cbalint13/m-blanc/hardware/mblanc_v0.3/kicad/m-blanc/3d-models/S25HL512TFANHI010.stp

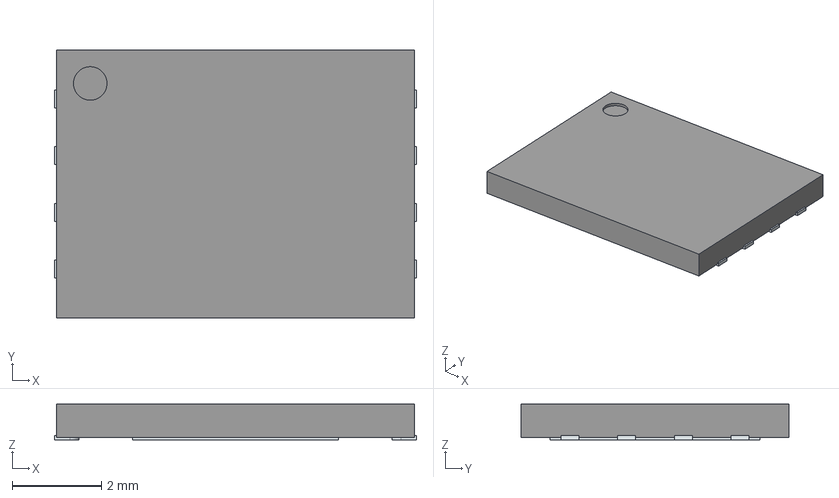
[picture p28: CAD file, 2022-12-04]
hardware/mblanc_v0.3/kicad/m-blanc/3d-models/S25HL512TFANHI010.stp
8.10 x 6.00 x 0.8 mm
ThermalPin
PinsArrayLR
