cbalint13/m-blanc/hardware/mblanc_v0.3/kicad/m-blanc/3d-models/step_temp.STEP

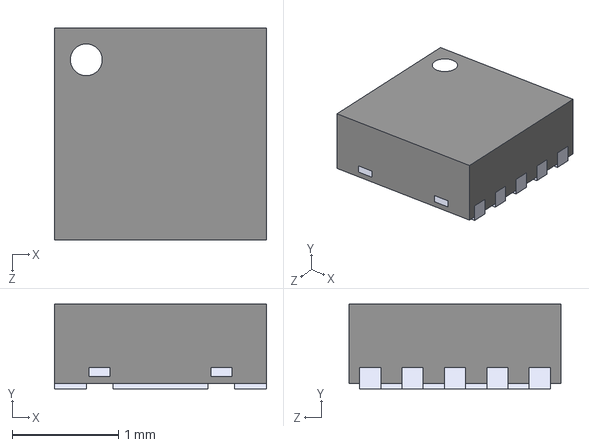
[picture p29: CAD file, 2022-12-04]
hardware/mblanc_v0.3/kicad/m-blanc/3d-models/step_temp.STEP
2.00 x 0.8 x 2.00 mm
