cbalint13/m-blanc/hardware/mblanc_v0.3/kicad/m-blanc/3d-models/74750-0021.stp

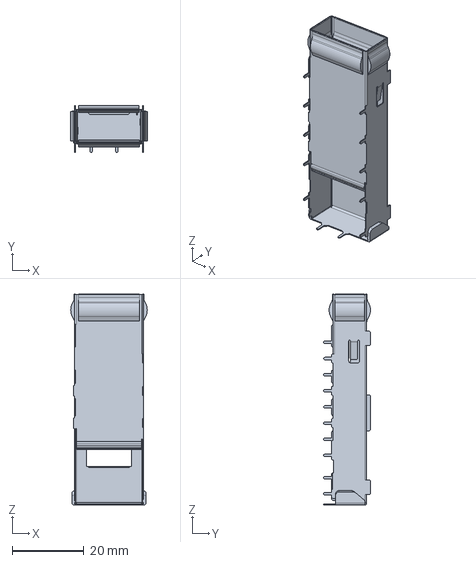
[picture p30: CAD file, 2022-12-04]
hardware/mblanc_v0.3/kicad/m-blanc/3d-models/74750-0021.stp
21.3 x 13.1 x 58.8 mm
