cbalint13/m-blanc/hardware/mblanc_v0.3/kicad/m-blanc/3d-models/296409204003856+.stp

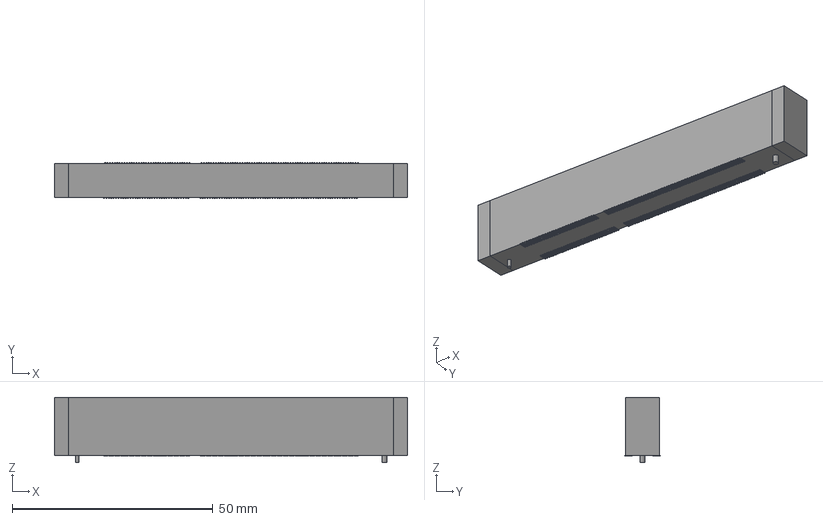
[picture p31: CAD file, 2022-12-04]
hardware/mblanc_v0.3/kicad/m-blanc/3d-models/296409204003856+.stp
88.0 x 8.93 x 16.3 mm
Pins
Lugs x 2
