cbalint13/m-blanc/hardware/mblanc_v0.3/kicad/m-blanc/schematic/2-MEMORY.kicad_sch

## KiCad design hardware/mblanc_v0.3/kicad/m-blanc/schematic/2-MEMORY.kicad_sch (2022-12-04)

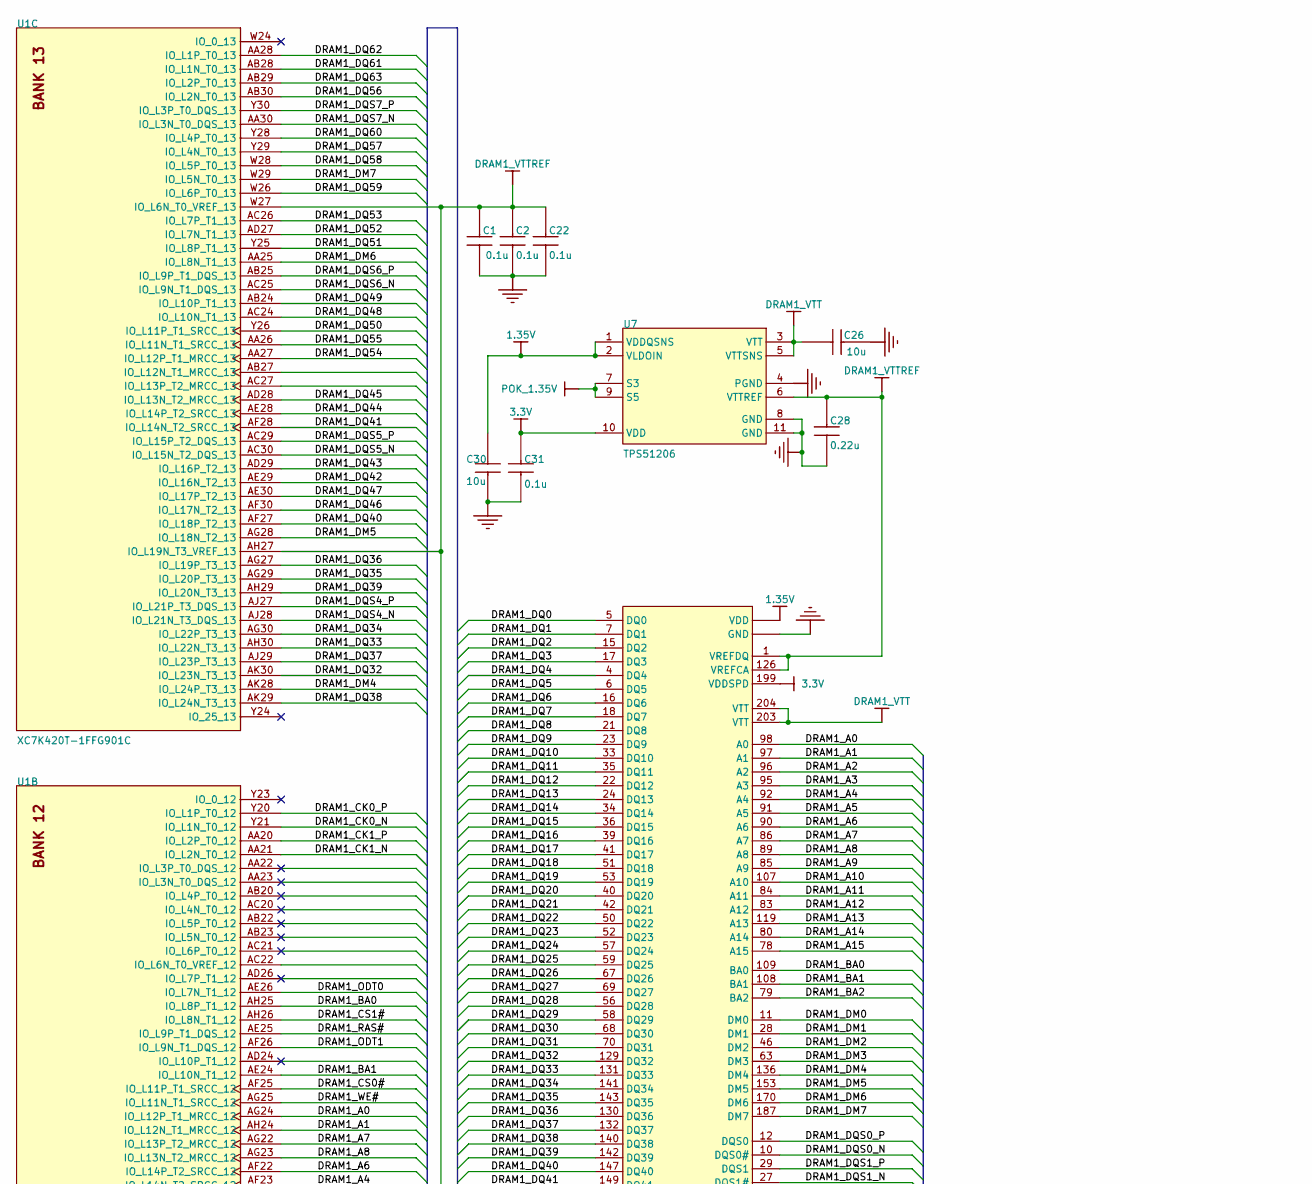
[picture p45: schematic 2-MEMORY.kicad_sch, part in row 1, column 1]

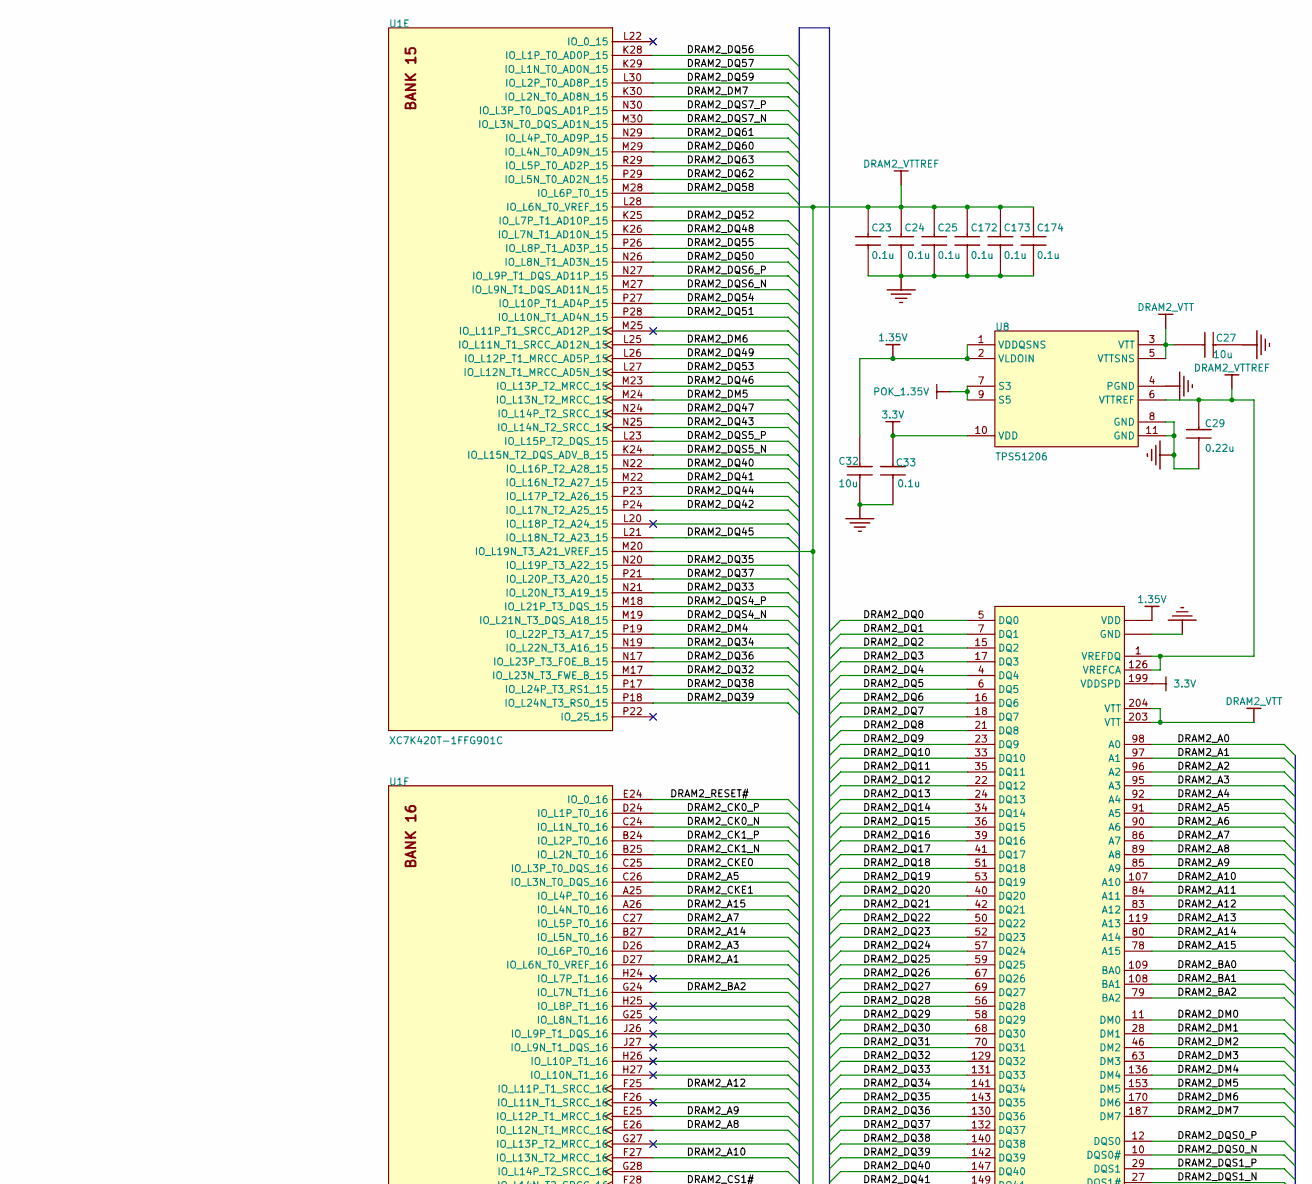
[picture p46: schematic 2-MEMORY.kicad_sch, part in row 1, column 2]

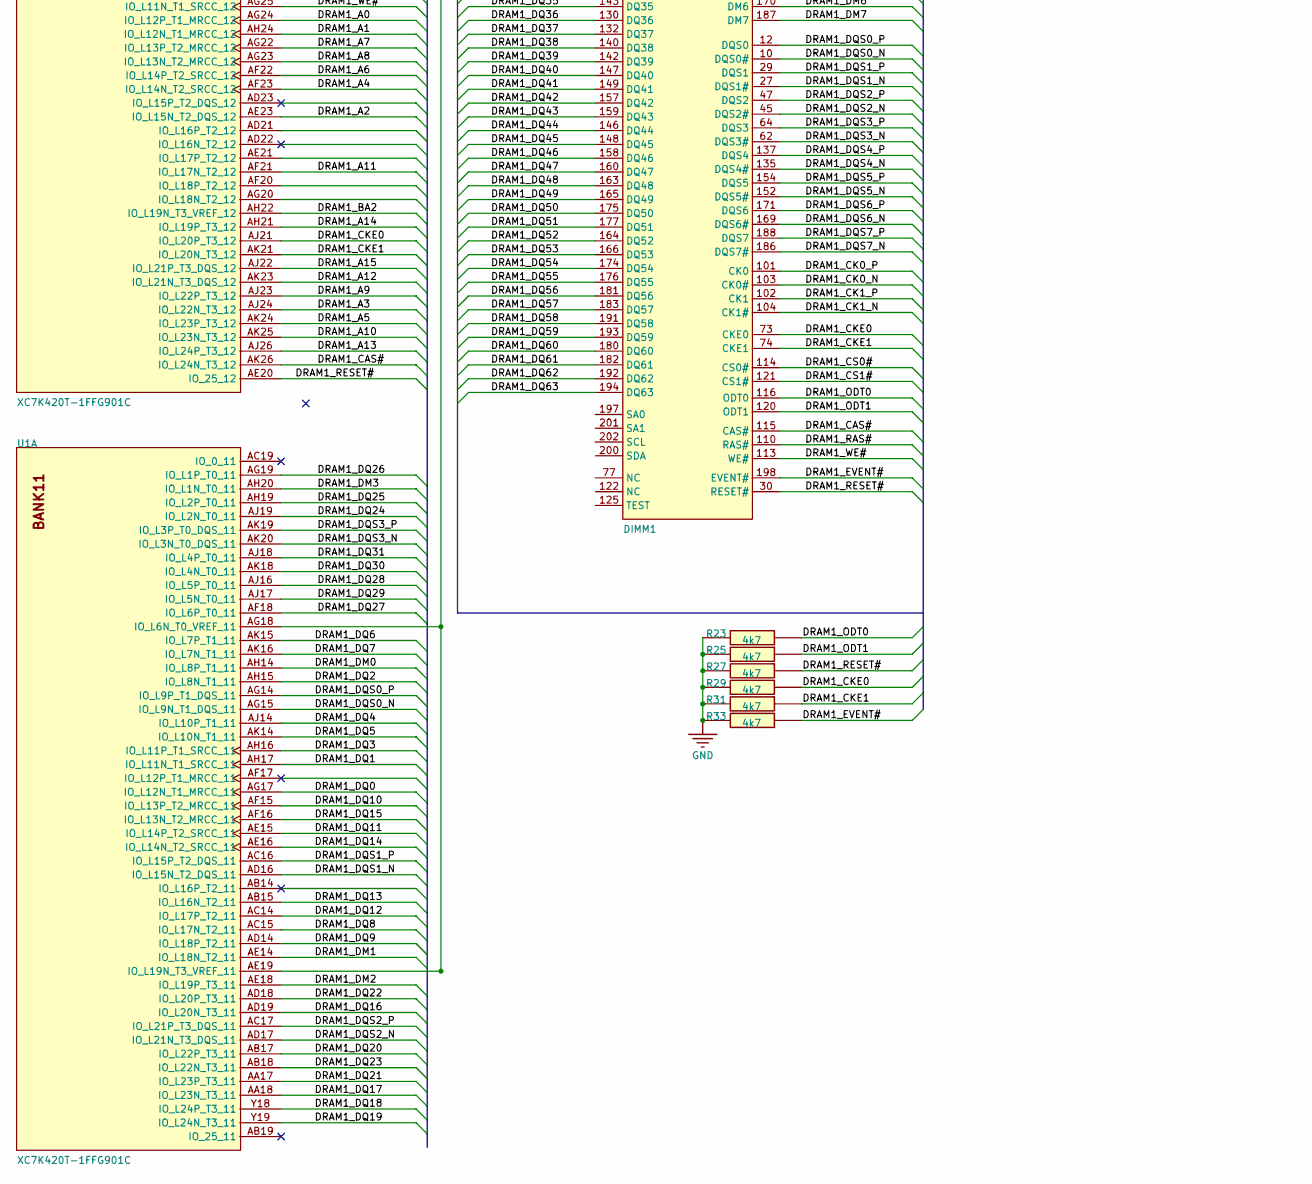
[picture p47: schematic 2-MEMORY.kicad_sch, part in row 2, column 1]

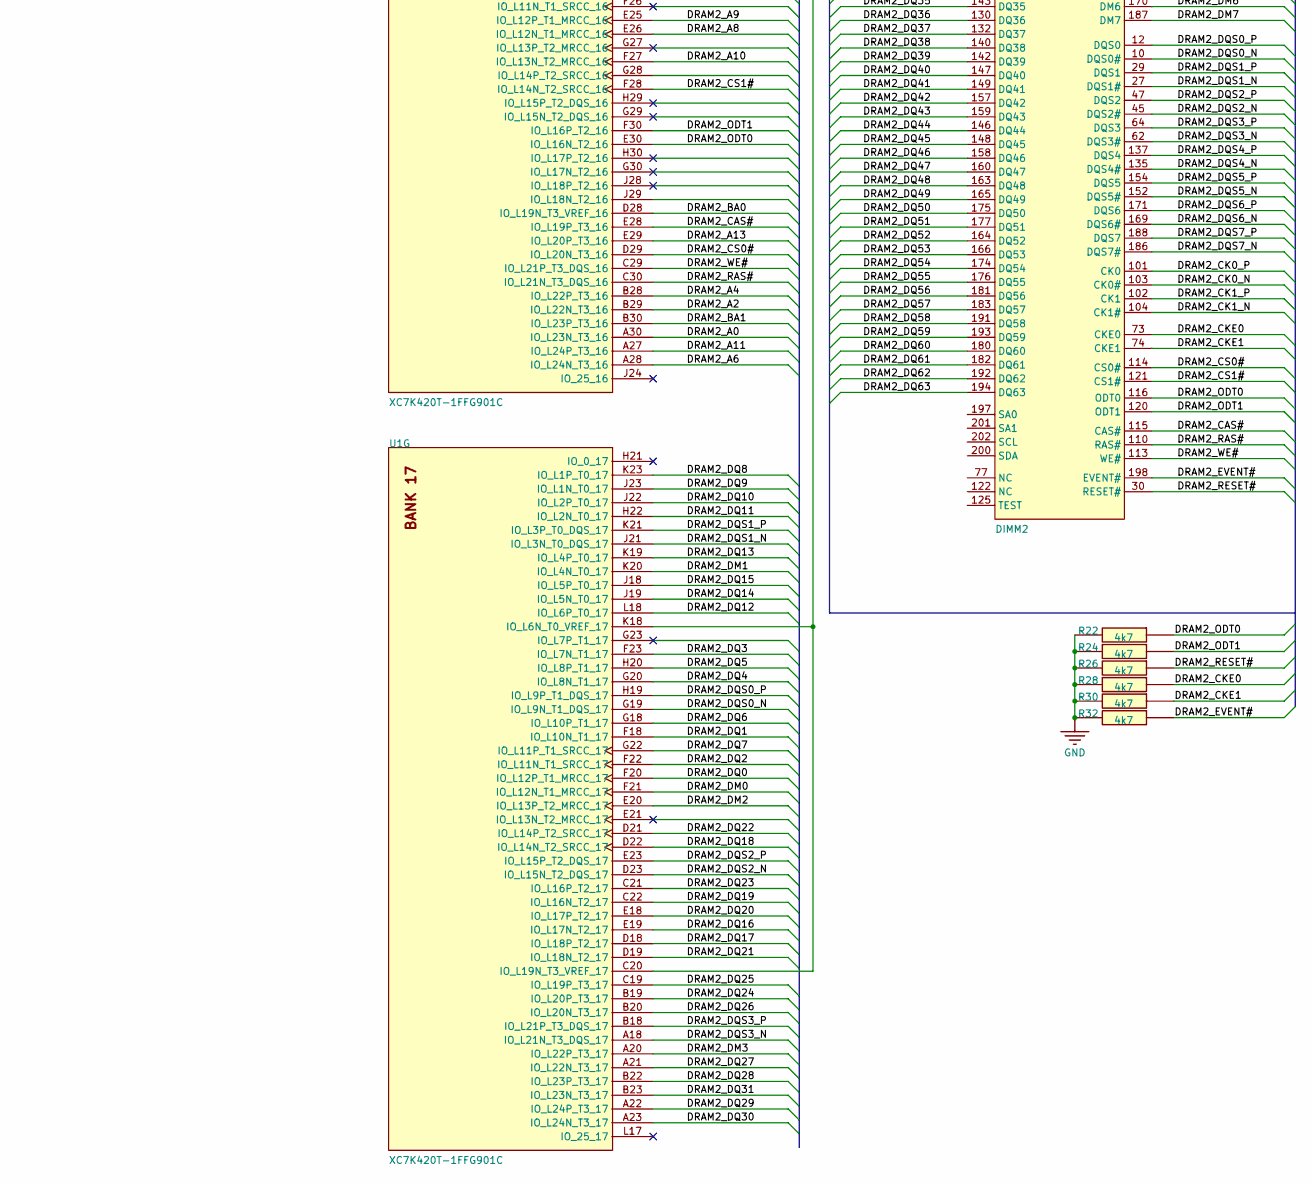
[picture p48: schematic 2-MEMORY.kicad_sch, part in row 2, column 2]

Parts:
C1, C2, C22, C23, C24, C25, C31, C33, C172, C173, C174: 0.1u; SMD0402
C26, C27, C30, C32: 10u; SMD0402
C28, C29: 0.22u; SMD0402
DIMM1, DIMM2: DDR3; 296409204003856
R22, R23, R24, R25, R26, R27, R28, R29, R30, R31, R32, R33: 4k7; SMD0402
U1: XC7K420T-1FFG901C; FFG901; PARTNUMBER XC7K420T-1FFG901C
U7, U8: TPS51206; SON40P200X200X80-11N

Connections:
DRAM1_A0: DIMM1.98 (A0)
DRAM1_A1: DIMM1.97 (A1)
DRAM1_A2: DIMM1.96 (A2)
DRAM1_A3: DIMM1.95 (A3)
DRAM1_A4: DIMM1.92 (A4)
DRAM1_A5: DIMM1.91 (A5)
DRAM1_A6: DIMM1.90 (A6)
DRAM1_A8: DIMM1.89 (A8)
DRAM1_A9: DIMM1.85 (A9)
DRAM1_A10: DIMM1.107 (A10)
DRAM1_A11: DIMM1.84 (A11)
DRAM1_A12: DIMM1.83 (A12)
DRAM1_A13: DIMM1.119 (A13)
DRAM1_A14: DIMM1.80 (A14)
DRAM1_A15: DIMM1.78 (A15)
DRAM1_BA0: DIMM1.109 (BA0)
DRAM1_BA1: DIMM1.108 (BA1)
DRAM1_BA2: DIMM1.79 (BA2)
DRAM1_CKE0: R29.1
DRAM1_CKE1: R31.1
DRAM1_DM0: DIMM1.11 (DM0)
DRAM1_DM1: DIMM1.28 (DM1)
DRAM1_DM2: DIMM1.46 (DM2)
DRAM1_DM3: DIMM1.63 (DM3)
DRAM1_DM4: DIMM1.136 (DM4), U1.AK28 (IO_L24P_T3_13)
DRAM1_DM5: DIMM1.153 (DM5)
DRAM1_DM6: DIMM1.170 (DM6), U1.AA25 (IO_L8N_T1_13)
DRAM1_DM7: DIMM1.187 (DM7), U1.W29 (IO_L5N_T0_13)
DRAM1_DQ0: DIMM1.5 (DQ0)
DRAM1_DQ1: DIMM1.7 (DQ1)
DRAM1_DQ2: DIMM1.15 (DQ2)
DRAM1_DQ3: DIMM1.17 (DQ3)
DRAM1_DQ4: DIMM1.4 (DQ4)
DRAM1_DQ5: DIMM1.6 (DQ5)
DRAM1_DQ6: DIMM1.16 (DQ6)
DRAM1_DQ7: DIMM1.18 (DQ7)
DRAM1_DQ8: DIMM1.21 (DQ8)
DRAM1_DQ9: DIMM1.23 (DQ9)
DRAM1_DQ10: DIMM1.33 (DQ10)
DRAM1_DQ11: DIMM1.35 (DQ11)
DRAM1_DQ12: DIMM1.22 (DQ12)
DRAM1_DQ13: DIMM1.24 (DQ13)
DRAM1_DQ14: DIMM1.34 (DQ14)
DRAM1_DQ15: DIMM1.36 (DQ15)
DRAM1_DQ16: DIMM1.39 (DQ16)
DRAM1_DQ17: DIMM1.41 (DQ17)
DRAM1_DQ18: DIMM1.51 (DQ18)
DRAM1_DQ19: DIMM1.53 (DQ19)
DRAM1_DQ20: DIMM1.40 (DQ20)
DRAM1_DQ21: DIMM1.42 (DQ21)
DRAM1_DQ22: DIMM1.50 (DQ22)
DRAM1_DQ23: DIMM1.52 (DQ23)
DRAM1_DQ24: DIMM1.57 (DQ24)
DRAM1_DQ25: DIMM1.59 (DQ25)
DRAM1_DQ26: DIMM1.67 (DQ26)
DRAM1_DQ27: DIMM1.69 (DQ27)
DRAM1_DQ28: DIMM1.56 (DQ28)
DRAM1_DQ29: DIMM1.58 (DQ29)
DRAM1_DQ30: DIMM1.68 (DQ30)
DRAM1_DQ31: DIMM1.70 (DQ31)
DRAM1_DQ32: DIMM1.129 (DQ32), U1.AK30 (IO_L23N_T3_13)
DRAM1_DQ33: DIMM1.131 (DQ33), U1.AH30 (IO_L22N_T3_13)
DRAM1_DQ34: DIMM1.141 (DQ34), U1.AG30 (IO_L22P_T3_13)
DRAM1_DQ35: DIMM1.143 (DQ35), U1.AG29 (IO_L20P_T3_13)
DRAM1_DQ36: DIMM1.130 (DQ36)
DRAM1_DQ37: DIMM1.132 (DQ37), U1.AJ29 (IO_L23P_T3_13)
DRAM1_DQ38: DIMM1.140 (DQ38), U1.AK29 (IO_L24N_T3_13)
DRAM1_DQ39: DIMM1.142 (DQ39), U1.AH29 (IO_L20N_T3_13)
DRAM1_DQ40: DIMM1.147 (DQ40), U1.AF27 (IO_L18P_T2_13)
DRAM1_DQ41: DIMM1.149 (DQ41), U1.AF28 (IO_L14N_T2_SRCC_13)
DRAM1_DQ42: DIMM1.157 (DQ42), U1.AE29 (IO_L16N_T2_13)
DRAM1_DQ43: DIMM1.159 (DQ43), U1.AD29 (IO_L16P_T2_13)
DRAM1_DQ44: DIMM1.146 (DQ44), U1.AE28 (IO_L14P_T2_SRCC_13)
DRAM1_DQ45: U1.AD28 (IO_L13N_T2_MRCC_13)
DRAM1_DQ46: U1.AF30 (IO_L17N_T2_13)
DRAM1_DQ47: U1.AE30 (IO_L17P_T2_13)
DRAM1_DQ48: U1.AC24 (IO_L10N_T1_13)
DRAM1_DQ49: U1.AB24 (IO_L10P_T1_13)
DRAM1_DQ50: U1.Y26 (IO_L11P_T1_SRCC_13)
DRAM1_DQ51: U1.Y25 (IO_L8P_T1_13)
DRAM1_DQ53: U1.AC26 (IO_L7P_T1_13)
DRAM1_DQ54: U1.AA27 (IO_L12P_T1_MRCC_13)
DRAM1_DQ55: U1.AA26 (IO_L11N_T1_SRCC_13)
DRAM1_DQ56: U1.AB30 (IO_L2N_T0_13)
DRAM1_DQ57: U1.Y29 (IO_L4N_T0_13)
DRAM1_DQ58: U1.W28 (IO_L5P_T0_13)
DRAM1_DQ59: U1.W26 (IO_L6P_T0_13)
DRAM1_DQ60: U1.Y28 (IO_L4P_T0_13)
DRAM1_DQ61: U1.AB28 (IO_L1N_T0_13)
DRAM1_DQ62: U1.AA28 (IO_L1P_T0_13)
DRAM1_DQ63: U1.AB29 (IO_L2P_T0_13)
DRAM1_DQS0_N: DIMM1.10 (DQS0#)
DRAM1_DQS0_P: DIMM1.12 (DQS0)
DRAM1_DQS1_N: DIMM1.27 (DQS1#)
DRAM1_DQS1_P: DIMM1.29 (DQS1)
DRAM1_DQS2_N: DIMM1.45 (DQS2#)
DRAM1_DQS2_P: DIMM1.47 (DQS2)
DRAM1_DQS3_N: DIMM1.62 (DQS3#)
DRAM1_DQS3_P: DIMM1.64 (DQS3)
DRAM1_DQS4_N: U1.AJ28 (IO_L21N_T3_DQS_13)
DRAM1_DQS4_P: U1.AJ27 (IO_L21P_T3_DQS_13)
DRAM1_DQS5_N: U1.AC30 (IO_L15N_T2_DQS_13)
DRAM1_DQS5_P: U1.AC29 (IO_L15P_T2_DQS_13)
DRAM1_DQS6_N: U1.AC25 (IO_L9N_T1_DQS_13)
DRAM1_DQS6_P: U1.AB25 (IO_L9P_T1_DQS_13)
DRAM1_DQS7_N: U1.AA30 (IO_L3N_T0_DQS_13)
DRAM1_DQS7_P: U1.Y30 (IO_L3P_T0_DQS_13)
DRAM1_EVENT#: R33.1
DRAM1_ODT0: R23.1
DRAM1_ODT1: R25.1
DRAM1_RESET#: R27.1
DRAM2_A0: DIMM2.98 (A0), U1.A30 (IO_L23N_T3_16)
DRAM2_A1: DIMM2.97 (A1), U1.D27 (IO_L6N_T0_VREF_16)
DRAM2_A2: DIMM2.96 (A2), U1.B29 (IO_L22N_T3_16)
DRAM2_A3: DIMM2.95 (A3), U1.D26 (IO_L6P_T0_16)
DRAM2_A4: DIMM2.92 (A4), U1.B28 (IO_L22P_T3_16)
DRAM2_A5: DIMM2.91 (A5), U1.C26 (IO_L3N_T0_DQS_16)
DRAM2_A6: DIMM2.90 (A6), U1.A28 (IO_L24N_T3_16)
DRAM2_A7: DIMM2.86 (A7), U1.C27 (IO_L5P_T0_16)
DRAM2_A8: DIMM2.89 (A8), U1.E26 (IO_L12N_T1_MRCC_16)
DRAM2_A9: DIMM2.85 (A9), U1.E25 (IO_L12P_T1_MRCC_16)
DRAM2_A10: DIMM2.107 (A10), U1.F27 (IO_L13N_T2_MRCC_16)
DRAM2_A11: DIMM2.84 (A11), U1.A27 (IO_L24P_T3_16)
DRAM2_A12: DIMM2.83 (A12), U1.F25 (IO_L11P_T1_SRCC_16)
DRAM2_A13: DIMM2.119 (A13), U1.E29 (IO_L20P_T3_16)
DRAM2_A14: DIMM2.80 (A14), U1.B27 (IO_L5N_T0_16)
DRAM2_A15: DIMM2.78 (A15), U1.A26 (IO_L4N_T0_16)
DRAM2_BA0: DIMM2.109 (BA0), U1.D28 (IO_L19N_T3_VREF_16)
DRAM2_BA1: DIMM2.108 (BA1), U1.B30 (IO_L23P_T3_16)
DRAM2_BA2: DIMM2.79 (BA2), U1.G24 (IO_L7N_T1_16)
DRAM2_CAS#: DIMM2.115 (CAS#), U1.E28 (IO_L19P_T3_16)
DRAM2_CK0_N: DIMM2.103 (CK0#), U1.C24 (IO_L1N_T0_16)
DRAM2_CK0_P: DIMM2.101 (CK0), U1.D24 (IO_L1P_T0_16)
DRAM2_CK1_N: DIMM2.104 (CK1#), U1.B25 (IO_L2N_T0_16)
DRAM2_CK1_P: DIMM2.102 (CK1), U1.B24 (IO_L2P_T0_16)
DRAM2_CKE0: DIMM2.73 (CKE0), R28.1, U1.C25 (IO_L3P_T0_DQS_16)
DRAM2_CKE1: DIMM2.74 (CKE1), R30.1, U1.A25 (IO_L4P_T0_16)
DRAM2_CS0#: DIMM2.114 (CS0#), U1.D29 (IO_L20N_T3_16)
DRAM2_CS1#: DIMM2.121 (CS1#), U1.F28 (IO_L14N_T2_SRCC_16)
DRAM2_DM0: DIMM2.11 (DM0)
DRAM2_DM1: DIMM2.28 (DM1)
DRAM2_DM2: DIMM2.46 (DM2)
DRAM2_DM3: DIMM2.63 (DM3)
DRAM2_DM4: DIMM2.136 (DM4), U1.P19 (IO_L22P_T3_A17_15)
DRAM2_DM5: DIMM2.153 (DM5), U1.M24 (IO_L13N_T2_MRCC_15)
DRAM2_DM6: DIMM2.170 (DM6), U1.L25 (IO_L11N_T1_SRCC_AD12N_15)
DRAM2_DM7: DIMM2.187 (DM7), U1.K30 (IO_L2N_T0_AD8N_15)
DRAM2_DQ0: DIMM2.5 (DQ0)
DRAM2_DQ1: DIMM2.7 (DQ1)
DRAM2_DQ2: DIMM2.15 (DQ2)
DRAM2_DQ3: DIMM2.17 (DQ3)
DRAM2_DQ4: DIMM2.4 (DQ4)
DRAM2_DQ5: DIMM2.6 (DQ5)
DRAM2_DQ6: DIMM2.16 (DQ6)
DRAM2_DQ7: DIMM2.18 (DQ7)
DRAM2_DQ8: DIMM2.21 (DQ8)
DRAM2_DQ9: DIMM2.23 (DQ9)
DRAM2_DQ10: DIMM2.33 (DQ10)
DRAM2_DQ11: DIMM2.35 (DQ11)
DRAM2_DQ12: DIMM2.22 (DQ12)
DRAM2_DQ13: DIMM2.24 (DQ13)
DRAM2_DQ14: DIMM2.34 (DQ14)
DRAM2_DQ15: DIMM2.36 (DQ15)
DRAM2_DQ16: DIMM2.39 (DQ16)
DRAM2_DQ17: DIMM2.41 (DQ17)
DRAM2_DQ18: DIMM2.51 (DQ18)
DRAM2_DQ19: DIMM2.53 (DQ19)
DRAM2_DQ20: DIMM2.40 (DQ20)
DRAM2_DQ21: DIMM2.42 (DQ21)
DRAM2_DQ22: DIMM2.50 (DQ22)
DRAM2_DQ23: DIMM2.52 (DQ23)
DRAM2_DQ24: DIMM2.57 (DQ24)
DRAM2_DQ25: DIMM2.59 (DQ25)
DRAM2_DQ26: DIMM2.67 (DQ26)
DRAM2_DQ27: DIMM2.69 (DQ27)
DRAM2_DQ28: DIMM2.56 (DQ28)
DRAM2_DQ29: DIMM2.58 (DQ29)
DRAM2_DQ30: DIMM2.68 (DQ30)
DRAM2_DQ31: DIMM2.70 (DQ31)
DRAM2_DQ32: DIMM2.129 (DQ32), U1.M17 (IO_L23N_T3_FWE_B_15)
DRAM2_DQ33: DIMM2.131 (DQ33), U1.N21 (IO_L20N_T3_A19_15)
DRAM2_DQ34: DIMM2.141 (DQ34), U1.N19 (IO_L22N_T3_A16_15)
DRAM2_DQ35: DIMM2.143 (DQ35), U1.N20 (IO_L19P_T3_A22_15)
DRAM2_DQ36: DIMM2.130 (DQ36), U1.N17 (IO_L23P_T3_FOE_B_15)
DRAM2_DQ37: DIMM2.132 (DQ37), U1.P21 (IO_L20P_T3_A20_15)
DRAM2_DQ38: DIMM2.140 (DQ38), U1.P17 (IO_L24P_T3_RS1_15)
DRAM2_DQ39: DIMM2.142 (DQ39), U1.P18 (IO_L24N_T3_RS0_15)
DRAM2_DQ40: DIMM2.147 (DQ40), U1.N22 (IO_L16P_T2_A28_15)
DRAM2_DQ41: DIMM2.149 (DQ41), U1.M22 (IO_L16N_T2_A27_15)
DRAM2_DQ42: DIMM2.157 (DQ42), U1.P24 (IO_L17N_T2_A25_15)
DRAM2_DQ43: DIMM2.159 (DQ43), U1.N25 (IO_L14N_T2_SRCC_15)
DRAM2_DQ44: DIMM2.146 (DQ44), U1.P23 (IO_L17P_T2_A26_15)
DRAM2_DQ45: DIMM2.148 (DQ45), U1.L21 (IO_L18N_T2_A23_15)
DRAM2_DQ46: DIMM2.158 (DQ46), U1.M23 (IO_L13P_T2_MRCC_15)
DRAM2_DQ47: DIMM2.160 (DQ47), U1.N24 (IO_L14P_T2_SRCC_15)
DRAM2_DQ48: DIMM2.163 (DQ48), U1.K26 (IO_L7N_T1_AD10N_15)
DRAM2_DQ49: DIMM2.165 (DQ49), U1.L26 (IO_L12P_T1_MRCC_AD5P_15)
DRAM2_DQ50: DIMM2.175 (DQ50), U1.N26 (IO_L8N_T1_AD3N_15)
DRAM2_DQ51: DIMM2.177 (DQ51), U1.P28 (IO_L10N_T1_AD4N_15)
DRAM2_DQ52: DIMM2.164 (DQ52), U1.K25 (IO_L7P_T1_AD10P_15)
DRAM2_DQ53: DIMM2.166 (DQ53)
DRAM2_DQ54: DIMM2.174 (DQ54), U1.P27 (IO_L10P_T1_AD4P_15)
DRAM2_DQ55: DIMM2.176 (DQ55), U1.P26 (IO_L8P_T1_AD3P_15)
DRAM2_DQ56: DIMM2.181 (DQ56), U1.K28 (IO_L1P_T0_AD0P_15)
DRAM2_DQ57: DIMM2.183 (DQ57), U1.K29 (IO_L1N_T0_AD0N_15)
DRAM2_DQ58: DIMM2.191 (DQ58), U1.M28 (IO_L6P_T0_15)
DRAM2_DQ59: DIMM2.193 (DQ59), U1.L30 (IO_L2P_T0_AD8P_15)
DRAM2_DQ60: DIMM2.180 (DQ60), U1.M29 (IO_L4N_T0_AD9N_15)
DRAM2_DQ61: DIMM2.182 (DQ61), U1.N29 (IO_L4P_T0_AD9P_15)
DRAM2_DQ62: DIMM2.192 (DQ62), U1.P29 (IO_L5N_T0_AD2N_15)
DRAM2_DQ63: DIMM2.194 (DQ63), U1.R29 (IO_L5P_T0_AD2P_15)
DRAM2_DQS0_N: DIMM2.10 (DQS0#)
DRAM2_DQS0_P: DIMM2.12 (DQS0)
DRAM2_DQS1_N: DIMM2.27 (DQS1#)
DRAM2_DQS1_P: DIMM2.29 (DQS1)
DRAM2_DQS2_N: DIMM2.45 (DQS2#)
DRAM2_DQS2_P: DIMM2.47 (DQS2)
DRAM2_DQS3_N: DIMM2.62 (DQS3#)
DRAM2_DQS3_P: DIMM2.64 (DQS3)
DRAM2_DQS4_N: DIMM2.135 (DQS4#), U1.M19 (IO_L21N_T3_DQS_A18_15)
DRAM2_DQS4_P: DIMM2.137 (DQS4), U1.M18 (IO_L21P_T3_DQS_15)
DRAM2_DQS5_N: DIMM2.152 (DQS5#), U1.K24 (IO_L15N_T2_DQS_ADV_B_15)
DRAM2_DQS5_P: DIMM2.154 (DQS5), U1.L23 (IO_L15P_T2_DQS_15)
DRAM2_DQS6_N: DIMM2.169 (DQS6#), U1.M27 (IO_L9N_T1_DQS_AD11N_15)
DRAM2_DQS6_P: DIMM2.171 (DQS6), U1.N27 (IO_L9P_T1_DQS_AD11P_15)
DRAM2_DQS7_N: DIMM2.186 (DQS7#), U1.M30 (IO_L3N_T0_DQS_AD1N_15)
DRAM2_DQS7_P: DIMM2.188 (DQS7), U1.N30 (IO_L3P_T0_DQS_AD1P_15)
DRAM2_EVENT#: DIMM2.198 (EVENT#), R32.1
DRAM2_ODT0: DIMM2.116 (ODT0), R22.1, U1.E30 (IO_L16N_T2_16)
DRAM2_ODT1: DIMM2.120 (ODT1), R24.1, U1.F30 (IO_L16P_T2_16)
DRAM2_RAS#: DIMM2.110 (RAS#), U1.C30 (IO_L21N_T3_DQS_16)
DRAM2_RESET#: DIMM2.30 (RESET#), R26.1, U1.E24 (IO_0_16)
DRAM2_WE#: DIMM2.113 (WE#), U1.C29 (IO_L21P_T3_DQS_16)
unnamed: C1.1, C2.1, C22.1
unnamed: C1.2, C2.2, C22.2, U1.AH27 (IO_L19N_T3_VREF_13), U1.W27 (IO_L6N_T0_VREF_13)
unnamed: C26.1, U7.3 (VTT), U7.5 (VTTSNS)
unnamed: C27.1, U8.3 (VTT), U8.5 (VTTSNS)
unnamed: C28.1, U7.8 (GND), U7.11 (GND)
unnamed: C28.2, DIMM1.1 (VREFDQ), DIMM1.126 (VREFCA), U7.6 (VTTREF)
unnamed: C29.1, U8.8 (GND), U8.11 (GND)
unnamed: C29.2, DIMM2.1 (VREFDQ), DIMM2.126 (VREFCA), U8.6 (VTTREF)
unnamed: C30.1, U7.1 (VDDQSNS), U7.2 (VLDOIN)
unnamed: C30.2, C31.2
unnamed: C31.1, U7.10 (VDD)
unnamed: C32.1, U8.1 (VDDQSNS), U8.2 (VLDOIN)
unnamed: C32.2, C33.2
unnamed: C33.1, U8.10 (VDD)
unnamed: C23.1, C24.1, C25.1, C172.1, C173.1, C174.1
unnamed: C23.2, C24.2, C25.2, C172.2, C173.2, C174.2, U1.L28 (IO_L6N_T0_VREF_15), U1.M20 (IO_L19N_T3_A21_VREF_15)
unnamed: DIMM1.75 (VDD), DIMM1.76 (VDD), DIMM1.81 (VDD), DIMM1.82 (VDD), DIMM1.87 (VDD), DIMM1.88 (VDD), DIMM1.93 (VDD), DIMM1.94 (VDD), DIMM1.99 (VDD), DIMM1.100 (VDD), DIMM1.105 (VDD), DIMM1.106 (VDD), DIMM1.111 (VDD), DIMM1.112 (VDD), DIMM1.117 (VDD), DIMM1.118 (VDD), DIMM1.123 (VDD), DIMM1.124 (VDD)
unnamed: DIMM1.2 (GND), DIMM1.3 (GND), DIMM1.8 (GND), DIMM1.9 (GND), DIMM1.13 (GND), DIMM1.14 (GND), DIMM1.19 (GND), DIMM1.20 (GND), DIMM1.25 (GND), DIMM1.26 (GND), DIMM1.31 (GND), DIMM1.32 (GND), DIMM1.37 (GND), DIMM1.38 (GND), DIMM1.43 (GND), DIMM1.44 (GND), DIMM1.48 (GND), DIMM1.49 (GND), DIMM1.54 (GND), DIMM1.55 (GND), DIMM1.60 (GND), DIMM1.61 (GND), DIMM1.65 (GND), DIMM1.66 (GND), DIMM1.71 (GND), DIMM1.72 (GND), DIMM1.127 (GND), DIMM1.128 (GND), DIMM1.133 (GND), DIMM1.134 (GND), DIMM1.138 (GND), DIMM1.139 (GND), DIMM1.144 (GND), DIMM1.145 (GND), DIMM1.150 (GND), DIMM1.151 (GND), DIMM1.155 (GND), DIMM1.156 (GND), DIMM1.161 (GND), DIMM1.162 (GND), DIMM1.167 (GND), DIMM1.168 (GND), DIMM1.172 (GND), DIMM1.173 (GND), DIMM1.178 (GND), DIMM1.179 (GND), DIMM1.184 (GND), DIMM1.185 (GND), DIMM1.189 (GND), DIMM1.190 (GND), DIMM1.195 (GND), DIMM1.196 (GND)
unnamed: DIMM1.203 (VTT), DIMM1.204 (VTT)
unnamed: DIMM2.75 (VDD), DIMM2.76 (VDD), DIMM2.81 (VDD), DIMM2.82 (VDD), DIMM2.87 (VDD), DIMM2.88 (VDD), DIMM2.93 (VDD), DIMM2.94 (VDD), DIMM2.99 (VDD), DIMM2.100 (VDD), DIMM2.105 (VDD), DIMM2.106 (VDD), DIMM2.111 (VDD), DIMM2.112 (VDD), DIMM2.117 (VDD), DIMM2.118 (VDD), DIMM2.123 (VDD), DIMM2.124 (VDD)
unnamed: DIMM2.2 (GND), DIMM2.3 (GND), DIMM2.8 (GND), DIMM2.9 (GND), DIMM2.13 (GND), DIMM2.14 (GND), DIMM2.19 (GND), DIMM2.20 (GND), DIMM2.25 (GND), DIMM2.26 (GND), DIMM2.31 (GND), DIMM2.32 (GND), DIMM2.37 (GND), DIMM2.38 (GND), DIMM2.43 (GND), DIMM2.44 (GND), DIMM2.48 (GND), DIMM2.49 (GND), DIMM2.54 (GND), DIMM2.55 (GND), DIMM2.60 (GND), DIMM2.61 (GND), DIMM2.65 (GND), DIMM2.66 (GND), DIMM2.71 (GND), DIMM2.72 (GND), DIMM2.127 (GND), DIMM2.128 (GND), DIMM2.133 (GND), DIMM2.134 (GND), DIMM2.138 (GND), DIMM2.139 (GND), DIMM2.144 (GND), DIMM2.145 (GND), DIMM2.150 (GND), DIMM2.151 (GND), DIMM2.155 (GND), DIMM2.156 (GND), DIMM2.161 (GND), DIMM2.162 (GND), DIMM2.167 (GND), DIMM2.168 (GND), DIMM2.172 (GND), DIMM2.173 (GND), DIMM2.178 (GND), DIMM2.179 (GND), DIMM2.184 (GND), DIMM2.185 (GND), DIMM2.189 (GND), DIMM2.190 (GND), DIMM2.195 (GND), DIMM2.196 (GND)
unnamed: DIMM2.203 (VTT), DIMM2.204 (VTT)
unnamed: R22.2, R24.2, R26.2, R28.2, R30.2, R32.2
unnamed: R23.2, R25.2, R27.2, R29.2, R31.2, R33.2
unnamed: U7.7 (S3), U7.9 (S5)
unnamed: U8.7 (S3), U8.9 (S5)
