cbalint13/m-blanc/hardware/mblanc_v0.3/kicad/m-blanc/schematic/3-FIFO.kicad_sch

## KiCad design hardware/mblanc_v0.3/kicad/m-blanc/schematic/3-FIFO.kicad_sch (2022-12-04)

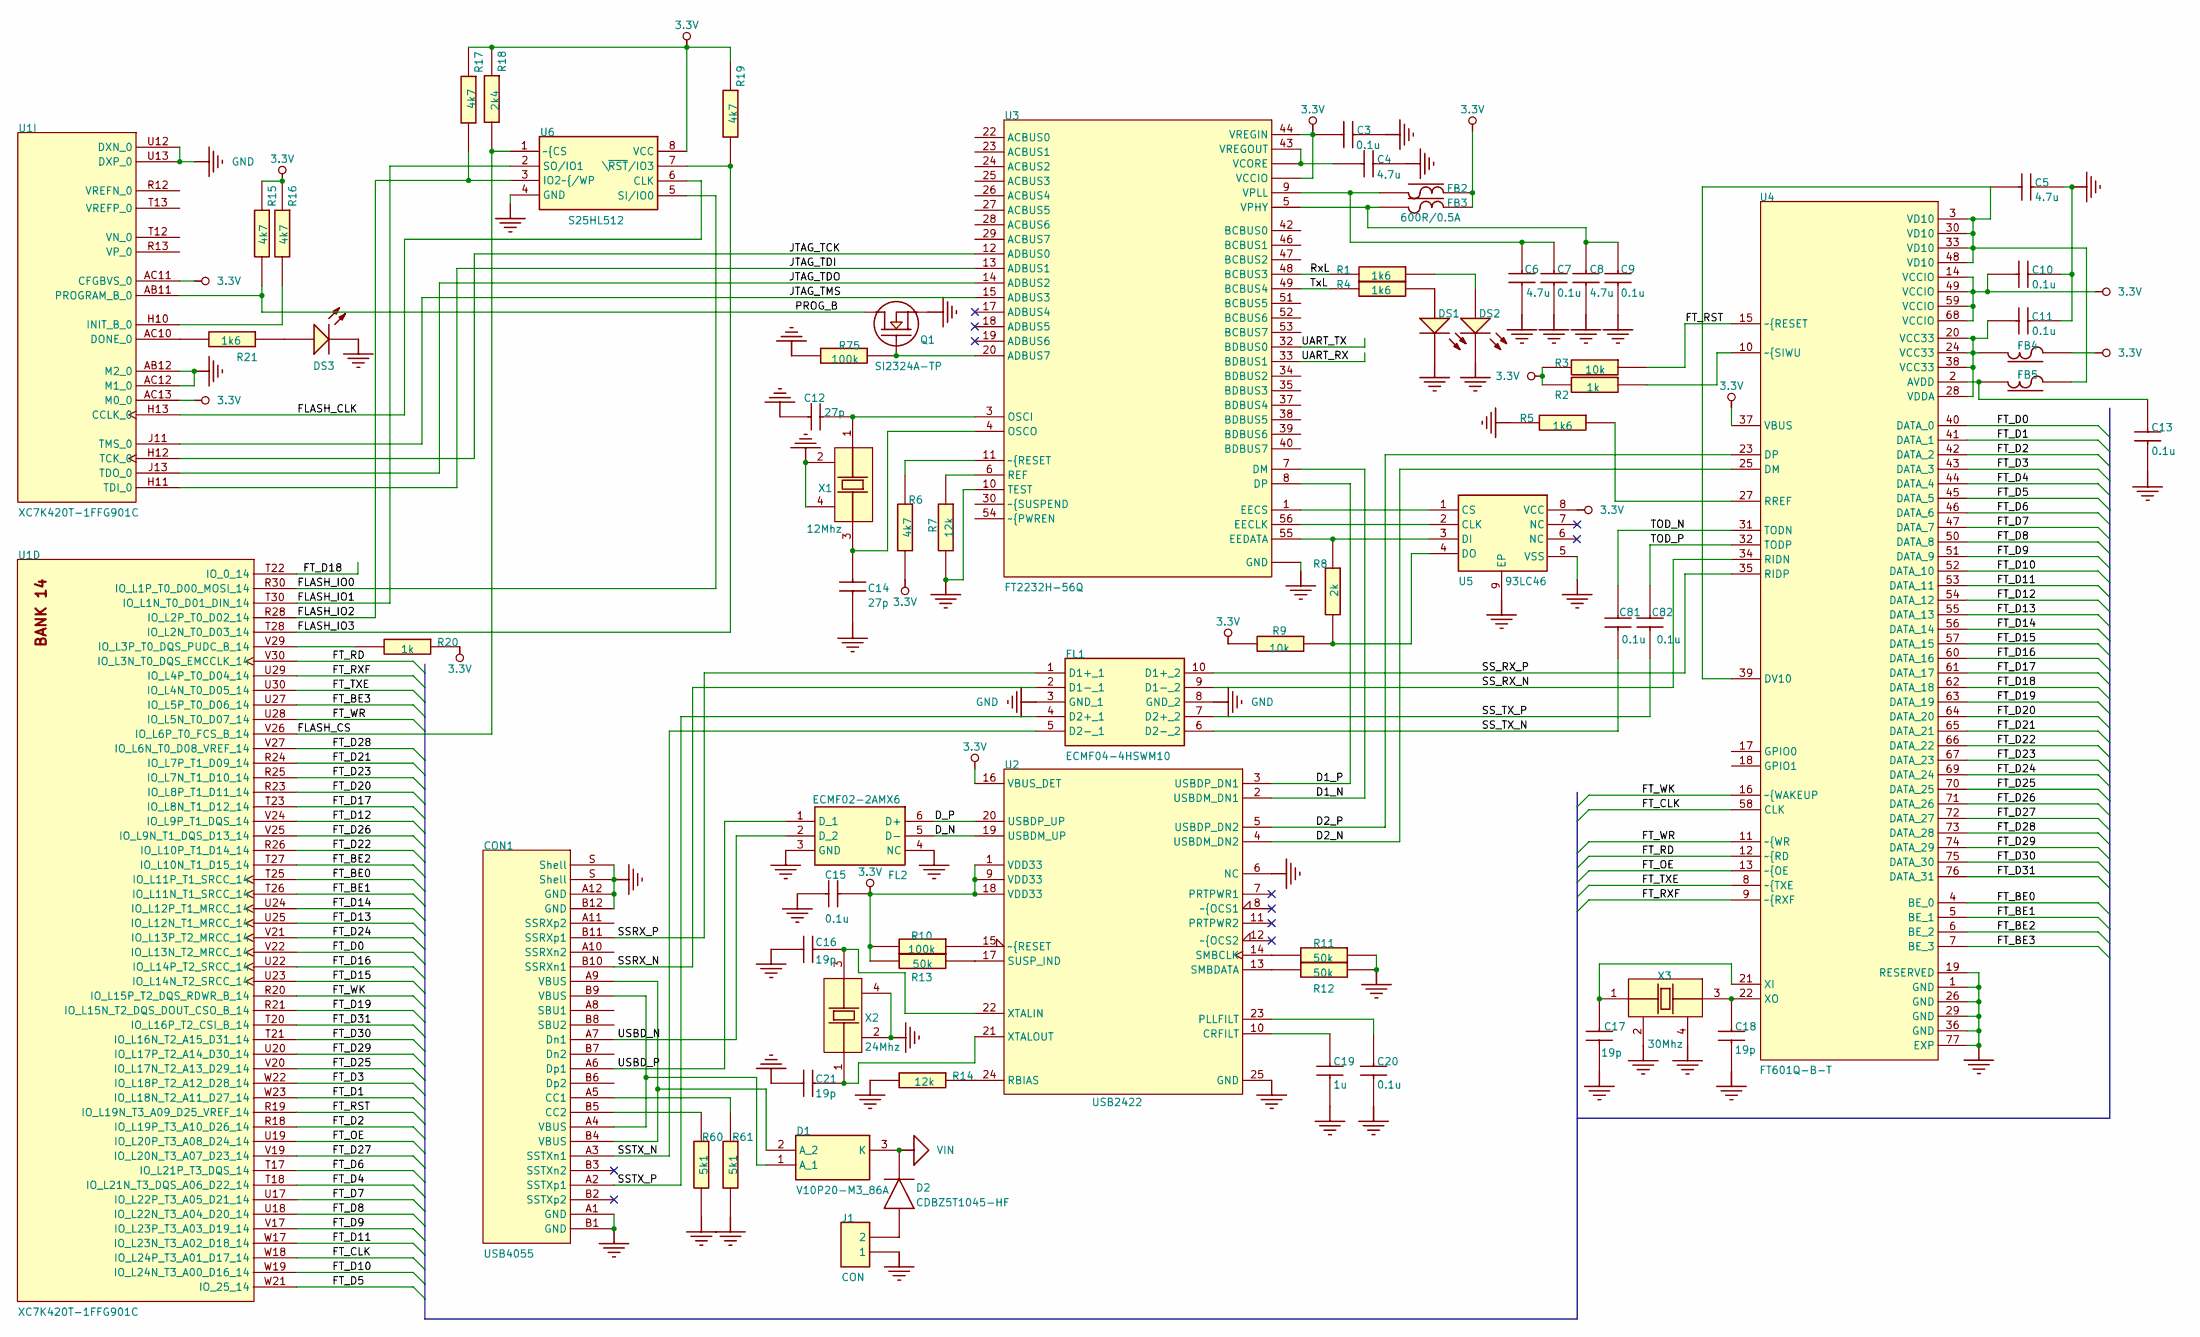
[picture p49: schematic 3-FIFO.kicad_sch]

Parts:
C3, C7, C9, C10, C11, C13, C15, C20, C81, C82: 0.1u; SMD0402
C4, C5, C6, C8: 4.7u; SMD0402
C12, C14: 27p; SMD0402
C16, C17, C18, C21: 19p; SMD0402
C19: 1u; SMD0402
CON1: USB4055; DX07S024JA2R1200
D1: V10P20-M3_86A; V10P20M386A; MANUFACTURER_PART_NUMBER V10P20-M3/86A; MOUSER PART NUMBER 78-V10P20-M3/86A
D2: CDBZ5T1045-HF; DIOM8060X543N; MANUFACTURER_PART_NUMBER SK106-TP; MOUSER PART NUMBER 833-SK106-TP
DS1, DS2, DS3: LED 0603; LED0603
FB2, FB3, FB4, FB5: 600R/0.5A; SMD0402
FL1: ECMF04-4HSWM10; SON50P135X260X55-10N-D; MANUFACTURER_PART_NUMBER ECMF04-4HSWM10; MOUSER PART NUMBER 511-ECMF04-4HSWM10
FL2: ECMF02-2AMX6; SON50P150X170X55-6N-D; MANUFACTURER_PART_NUMBER ECMF02-2AMX6; MOUSER PART NUMBER 511-ECMF02-2AMX6
J1: CON; TB00650802BE; MANUFACTURER_PART_NUMBER TB006-508-02BE; MOUSER PART NUMBER 490-TB006-508-02BE
Q1: SI2324A-TP; SI2305TP; MANUFACTURER_PART_NUMBER SI2324A-TP; MOUSER PART NUMBER 833-SI2324A-TP
R1, R4, R5, R21: 1k6; SMD0402
R2, R20: 1k; SMD0402
R3, R9: 10k; SMD0402
R6, R15, R16, R17, R19: 4k7; SMD0402
R7, R14: 12k; SMD0402
R8: 2k; SMD0402
R10, R75: 100k; SMD0402
R11, R12, R13: 50k; SMD0402
R18: 2k4; SMD0402
R60, R61: 5k1; SMD0402
U1: XC7K420T-1FFG901C; FFG901; PARTNUMBER XC7K420T-1FFG901C
U2: USB2422; QFN-MJ24
U3: FT2232H-56Q; QFN50P800X800X100-57N-D
U4: FT601Q-B-T; *QFN40P900X900X100-77N
U5: 93LC46; *SON50P200X300X100-9N
U6: S25HL512; SON127P800X600X80-9N-D
X1: 12Mhz; CRYSTAL2520
X2: 24Mhz; CRYSTAL1210
X3: 30Mhz; CRYSTAL1210

Connections:
D1_N: U2.2 (USBDM_DN1), U3.7 (DM)
D1_P: U2.3 (USBDP_DN1), U3.8 (DP)
D2_N: U2.4 (USBDM_DN2), U4.25 (DM)
D2_P: U2.5 (USBDP_DN2), U4.23 (DP)
D_N: FL2.5 (D-), U2.19 (USBDM_UP)
D_P: FL2.6 (D+), U2.20 (USBDP_UP)
FLASH_CLK: U1.H13 (CCLK_0), U6.6 (CLK)
FLASH_CS: R18.1, U1.V26 (IO_L6P_T0_FCS_B_14), U6.1 (~{CS)
FLASH_IO0: U1.R30 (IO_L1P_T0_D00_MOSI_14), U6.5 (SI/IO0)
FLASH_IO1: U1.T30 (IO_L1N_T0_D01_DIN_14), U6.2 (SO/IO1)
FLASH_IO2: R17.1, U1.R28 (IO_L2P_T0_D02_14), U6.3 (IO2~{/WP)
FLASH_IO3: R19.1, U1.T28 (IO_L2N_T0_D03_14), U6.7 (\~RST/IO3)
FT_BE0: U1.T25 (IO_L11P_T1_SRCC_14), U4.4 (BE_0)
FT_BE1: U1.T26 (IO_L11N_T1_SRCC_14), U4.5 (BE_1)
FT_BE2: U1.T27 (IO_L10N_T1_D15_14), U4.6 (BE_2)
FT_BE3: U1.U27 (IO_L5P_T0_D06_14), U4.7 (BE_3)
FT_CLK: U1.W18 (IO_L24P_T3_A01_D17_14), U4.58 (CLK)
FT_D0: U1.V22 (IO_L13N_T2_MRCC_14), U4.40 (DATA_0)
FT_D1: U1.W23 (IO_L18N_T2_A11_D27_14), U4.41 (DATA_1)
FT_D2: U1.R18 (IO_L19P_T3_A10_D26_14), U4.42 (DATA_2)
FT_D3: U1.W22 (IO_L18P_T2_A12_D28_14), U4.43 (DATA_3)
FT_D4: U1.T18 (IO_L21N_T3_DQS_A06_D22_14), U4.44 (DATA_4)
FT_D5: U1.W21 (IO_25_14), U4.45 (DATA_5)
FT_D6: U1.T17 (IO_L21P_T3_DQS_14), U4.46 (DATA_6)
FT_D7: U1.U17 (IO_L22P_T3_A05_D21_14), U4.47 (DATA_7)
FT_D8: U1.U18 (IO_L22N_T3_A04_D20_14), U4.50 (DATA_8)
FT_D9: U1.V17 (IO_L23P_T3_A03_D19_14), U4.51 (DATA_9)
FT_D10: U1.W19 (IO_L24N_T3_A00_D16_14), U4.52 (DATA_10)
FT_D11: U1.W17 (IO_L23N_T3_A02_D18_14), U4.53 (DATA_11)
FT_D12: U1.V24 (IO_L9P_T1_DQS_14), U4.54 (DATA_12)
FT_D13: U1.U25 (IO_L12N_T1_MRCC_14), U4.55 (DATA_13)
FT_D14: U1.U24 (IO_L12P_T1_MRCC_14), U4.56 (DATA_14)
FT_D15: U1.U23 (IO_L14N_T2_SRCC_14), U4.57 (DATA_15)
FT_D16: U1.U22 (IO_L14P_T2_SRCC_14), U4.60 (DATA_16)
FT_D17: U1.T23 (IO_L8N_T1_D12_14), U4.61 (DATA_17)
FT_D18: U1.T22 (IO_0_14), U4.62 (DATA_18)
FT_D19: U1.R21 (IO_L15N_T2_DQS_DOUT_CSO_B_14), U4.63 (DATA_19)
FT_D20: U1.R23 (IO_L8P_T1_D11_14), U4.64 (DATA_20)
FT_D21: U1.R24 (IO_L7P_T1_D09_14), U4.65 (DATA_21)
FT_D22: U1.R26 (IO_L10P_T1_D14_14), U4.66 (DATA_22)
FT_D23: U1.R25 (IO_L7N_T1_D10_14), U4.67 (DATA_23)
FT_D24: U1.V21 (IO_L13P_T2_MRCC_14), U4.69 (DATA_24)
FT_D25: U1.V20 (IO_L17N_T2_A13_D29_14), U4.70 (DATA_25)
FT_D26: U1.V25 (IO_L9N_T1_DQS_D13_14), U4.71 (DATA_26)
FT_D27: U1.V19 (IO_L20N_T3_A07_D23_14), U4.72 (DATA_27)
FT_D28: U1.V27 (IO_L6N_T0_D08_VREF_14), U4.73 (DATA_28)
FT_D29: U1.U20 (IO_L17P_T2_A14_D30_14), U4.74 (DATA_29)
FT_D30: U1.T21 (IO_L16N_T2_A15_D31_14), U4.75 (DATA_30)
FT_D31: U1.T20 (IO_L16P_T2_CSI_B_14), U4.76 (DATA_31)
FT_OE: U1.U19 (IO_L20P_T3_A08_D24_14), U4.13 (~{OE)
FT_RD: U1.V30 (IO_L3N_T0_DQS_EMCCLK_14), U4.12 (~{RD)
FT_RST: R3.2, U1.R19 (IO_L19N_T3_A09_D25_VREF_14), U4.15 (~{RESET)
FT_RXF: U1.U29 (IO_L4P_T0_D04_14), U4.9 (~{RXF)
FT_TXE: U1.U30 (IO_L4N_T0_D05_14), U4.8 (~{TXE)
FT_WK: U1.R20 (IO_L15P_T2_DQS_RDWR_B_14), U4.16 (~{WAKEUP)
FT_WR: U1.U28 (IO_L5N_T0_D07_14), U4.11 (~{WR)
JTAG_TCK: U1.H12 (TCK_0), U3.12 (ADBUS0)
unnamed: C6.2, C7.2, FB2.1, U3.9 (VPLL)
unnamed: C8.2, C9.2, FB3.1, U3.5 (VPHY)
unnamed: C5.1, C10.1, C11.1
unnamed: C12.1, U3.3 (OSCI), X1.1 (X1)
unnamed: C13.1, FB5.2, U4.2 (AVDD)
unnamed: C14.2, U3.4 (OSCO), X1.3 (X2)
unnamed: C15.1, R10.1, R13.1, U2.1 (VDD33), U2.9 (VDD33), U2.18 (VDD33)
unnamed: C16.2, U2.22 (XTALIN), X2.3 (X2)
unnamed: C17.1, U4.21 (XI), X3.1 (X1)
unnamed: C18.1, U4.22 (XO), X3.3 (X2)
unnamed: C19.1, U2.10 (CRFILT)
unnamed: C20.1, U2.23 (PLLFILT)
unnamed: C21.2, U2.21 (XTALOUT), X2.1 (X1)
unnamed: CON1.A1 (GND), CON1.B1 (GND)
unnamed: CON1.A4 (VBUS), CON1.B9 (VBUS), D1.1 (A_1)
unnamed: CON1.A5 (CC1), R61.2
unnamed: CON1.A9 (VBUS), CON1.B4 (VBUS), D1.2 (A_2)
unnamed: CON1.A12 (GND), CON1.B12 (GND), CON1.S (Shell)
unnamed: CON1.B5 (CC2), R60.2
unnamed: D1.3 (K), D2.1 (K)
unnamed: DS1.1 (A), R4.1
unnamed: DS2.1 (A), R1.1
unnamed: DS3.1 (A), R21.1
unnamed: FB2.2, FB3.2
unnamed: FB4.2, U4.20 (VCC33), U4.24 (VCC33), U4.28 (VDDA), U4.38 (VCC33)
unnamed: FB5.1, U4.3 (VD10), U4.30 (VD10), U4.33 (VD10), U4.39 (DV10), U4.48 (VD10)
unnamed: Q1.1 (G), R75.1, U3.20 (ADBUS7)
unnamed: R2.1, U4.10 (~{SIWU)
unnamed: R5.1, U4.27 (RREF)
unnamed: R6.2, U3.11 (~{RESET)
unnamed: R7.1, U3.10 (TEST)
unnamed: R7.2, U3.6 (REF)
unnamed: R8.1, U3.55 (EEDATA), U5.3 (DI)
unnamed: R8.2, R9.1, U5.4 (DO)
unnamed: R10.2, U2.15 (~{RESET)
unnamed: R11.1, U2.14 (SMBCLK)
unnamed: R11.2, R12.2
unnamed: R12.1, U2.13 (SMBDATA)
unnamed: R13.2, U2.17 (SUSP_IND)
unnamed: R14.2, U2.24 (RBIAS)
unnamed: R15.2, R16.2
unnamed: R16.1, U1.H10 (INIT_B_0)
unnamed: R17.2, R18.2, R19.2, U6.8 (VCC)
unnamed: R20.1, U1.V29 (IO_L3P_T0_DQS_PUDC_B_14)
unnamed: R21.2, U1.AC10 (DONE_0)
unnamed: U1.AB12 (M2_0), U1.AC12 (M1_0)
unnamed: U1.H11 (TDI_0), U3.13 (ADBUS1)
unnamed: U1.J11 (TMS_0), U3.15 (ADBUS3)
unnamed: U1.J13 (TDO_0), U3.14 (ADBUS2)
unnamed: U1.U12 (DXN_0), U1.U13 (DXP_0)
unnamed: U3.1 (EECS), U5.1 (CS)
unnamed: U3.2 (VCORE), U3.31 (VCORE), U3.43 (VREGOUT)
unnamed: U3.16 (VCCIO), U3.36 (VCCIO), U3.44 (VREGIN), U3.50 (VCCIO)
unnamed: U3.21 (GND), U3.41 (GND), U3.45 (GND), U3.57 (GND)
unnamed: U3.56 (EECLK), U5.2 (CLK)
unnamed: U4.1 (GND), U4.19 (RESERVED), U4.26 (GND), U4.29 (GND), U4.36 (GND), U4.77 (EXP)
unnamed: U4.14 (VCCIO), U4.49 (VCCIO), U4.59 (VCCIO), U4.68 (VCCIO)
unnamed: X1.2 (GND), X1.4 (GND)
unnamed: X2.2 (GND), X2.4 (GND)
PROG_B: Q1.3 (D), R15.1, U1.AB11 (PROGRAM_B_0)
RxL: U3.48 (BCBUS3)
SSRX_N: CON1.B10 (SSRXn1), FL1.2 (D1-_1)
SSRX_P: CON1.B11 (SSRXp1), FL1.1 (D1+_1)
SSTX_N: CON1.A3 (SSTXn1), FL1.5 (D2-_1)
SSTX_P: CON1.A2 (SSTXp1), FL1.4 (D2+_1)
SS_RX_N: FL1.9 (D1-_2), U4.34 (RIDN)
SS_RX_P: FL1.10 (D1+_2), U4.35 (RIDP)
SS_TX_N: C81.2, FL1.6 (D2-_2)
SS_TX_P: C82.2, FL1.7 (D2+_2)
TOD_N: C81.1, U4.31 (TODN)
TOD_P: C82.1, U4.32 (TODP)
TxL: U3.49 (BCBUS4)
UART_RX: U3.33 (BDBUS1)
UART_TX: U3.32 (BDBUS0)
USBD_N: CON1.A7 (Dn1), FL2.2 (D_2)
USBD_P: CON1.A6 (Dp1), FL2.1 (D_1)
