cbalint13/m-blanc/hardware/mblanc_v0.3/kicad/m-blanc/schematic/4-PCIe.kicad_sch

## KiCad design hardware/mblanc_v0.3/kicad/m-blanc/schematic/4-PCIe.kicad_sch (2022-12-04)

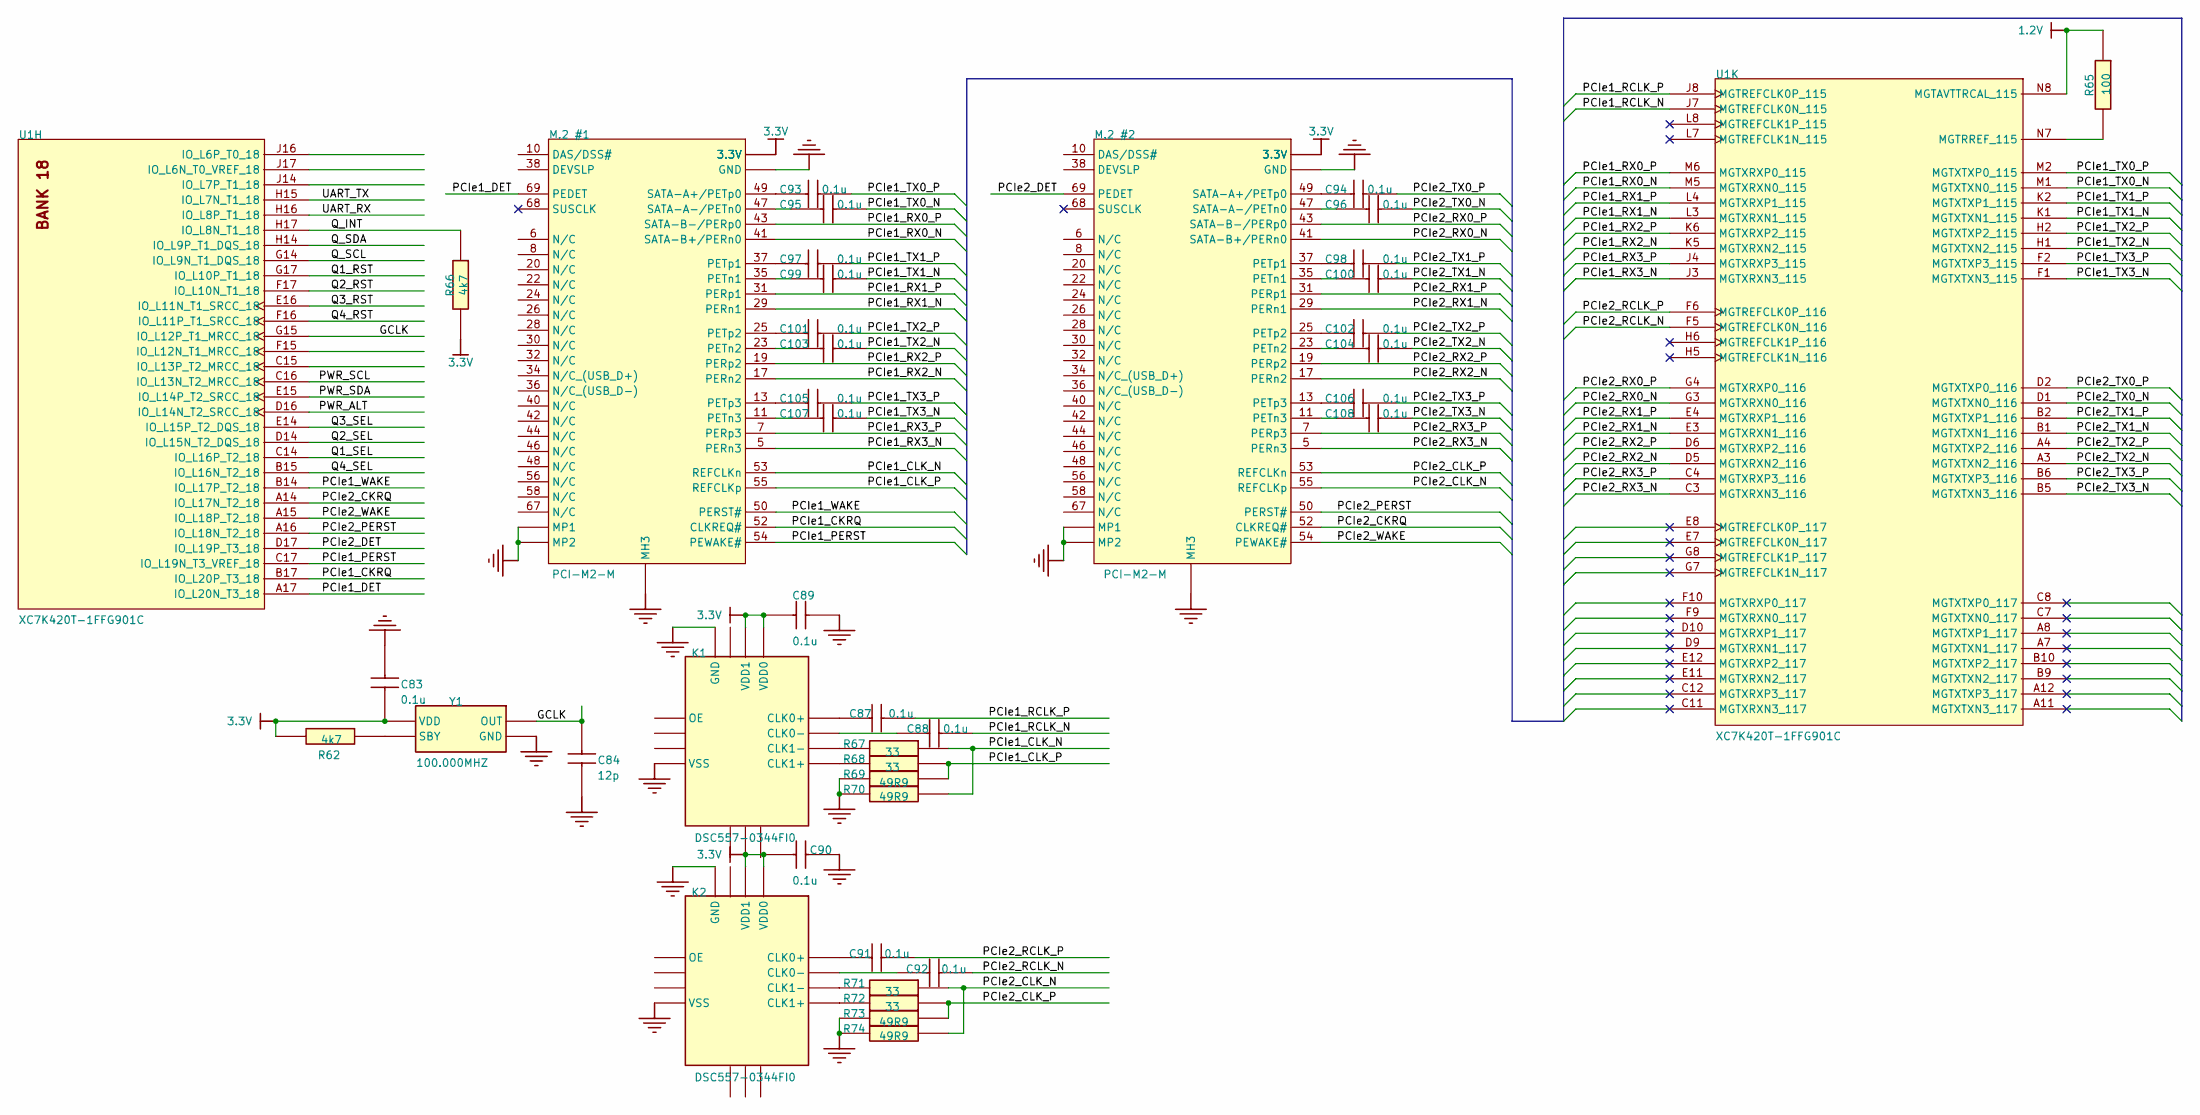
[picture p50: schematic 4-PCIe.kicad_sch]

Parts:
C83, C87, C88, C89, C90, C91, C92, C93, C94, C95, C96, C97, C98, C99, C100, C101, C102, C103, C104, C105, C106, C107, C108: 0.1u; SMD0402
C84: 12p; SMD0402
K1, K2: DSC557-0344FI0; QFN50P250X320X90-15N; MANUFACTURER_PART_NUMBER DSC557-0344FI0; MOUSER PART NUMBER 998-DSC557-0344FI0
M.2 #1, M.2 #2: PCI-M2-M; PCIE-M2-M; MANUFACTURER_PART_NUMBER MDT275M02001
R62, R66: 4k7; SMD0402
R65: 100; SMD0402
R67, R68, R71, R72: 33; SMD0402
R69, R70, R73, R74: 49R9; SMD0402
U1: XC7K420T-1FFG901C; FFG901; PARTNUMBER XC7K420T-1FFG901C
Y1: 100.000MHZ; ASEM1100000MHZLCT; MANUFACTURER_PART_NUMBER ASEM1-100.000MHZ-L-C-T; MOUSER PART NUMBER 815-ASEM1-100.0-LCT

Connections:
GCLK: C84.2, U1.G15 (IO_L12P_T1_MRCC_18), Y1.3 (OUT)
unnamed: C83.1, R62.1, Y1.4 (VDD)
unnamed: C87.2, K1.11 (CLK0+)
unnamed: C88.2, K1.10 (CLK0-)
unnamed: C89.2, K1.12 (VDD0), K1.13 (VDD1)
unnamed: C90.2, K2.12 (VDD0), K2.13 (VDD1)
unnamed: C91.2, K2.11 (CLK0+)
unnamed: C92.2, K2.10 (CLK0-)
unnamed: C93.2, M.2 #1.49 (SATA-A+/PETp0)
unnamed: C94.2, M.2 #2.49 (SATA-A+/PETp0)
unnamed: C95.2, M.2 #1.47 (SATA-A-/PETn0)
unnamed: C96.2, M.2 #2.47 (SATA-A-/PETn0)
unnamed: C97.2, M.2 #1.37 (PETp1)
unnamed: C98.2, M.2 #2.37 (PETp1)
unnamed: C99.2, M.2 #1.35 (PETn1)
unnamed: C100.2, M.2 #2.35 (PETn1)
unnamed: C101.2, M.2 #1.25 (PETp2)
unnamed: C102.2, M.2 #2.25 (PETp2)
unnamed: C103.2, M.2 #1.23 (PETn2)
unnamed: C104.2, M.2 #2.23 (PETn2)
unnamed: C105.2, M.2 #1.13 (PETp3)
unnamed: C106.2, M.2 #2.13 (PETp3)
unnamed: C107.2, M.2 #1.11 (PETn3)
unnamed: C108.2, M.2 #2.11 (PETn3)
unnamed: K1.8 (CLK1+), R68.2
unnamed: K1.9 (CLK1-), R67.2
unnamed: K2.8 (CLK1+), R72.2
unnamed: K2.9 (CLK1-), R71.2
unnamed: M.2 #1.1 (GND), M.2 #1.3 (GND), M.2 #1.9 (GND), M.2 #1.15 (GND), M.2 #1.21 (GND), M.2 #1.27 (GND), M.2 #1.33 (GND), M.2 #1.39 (GND), M.2 #1.45 (GND), M.2 #1.51 (GND), M.2 #1.57 (GND), M.2 #1.71 (GND), M.2 #1.73 (GND), M.2 #1.75 (GND)
unnamed: M.2 #1.2 (3.3V), M.2 #1.4 (3.3V), M.2 #1.12 (3.3V), M.2 #1.14 (3.3V), M.2 #1.16 (3.3V), M.2 #1.18 (3.3V)
unnamed: M.2 #1.70 (3.3V), M.2 #1.72 (3.3V), M.2 #1.74 (3.3V)
unnamed: M.2 #1.MP1, M.2 #1.MP2
unnamed: M.2 #2.1 (GND), M.2 #2.3 (GND), M.2 #2.9 (GND), M.2 #2.15 (GND), M.2 #2.21 (GND), M.2 #2.27 (GND), M.2 #2.33 (GND), M.2 #2.39 (GND), M.2 #2.45 (GND), M.2 #2.51 (GND), M.2 #2.57 (GND), M.2 #2.71 (GND), M.2 #2.73 (GND), M.2 #2.75 (GND)
unnamed: M.2 #2.2 (3.3V), M.2 #2.4 (3.3V), M.2 #2.12 (3.3V), M.2 #2.14 (3.3V), M.2 #2.16 (3.3V), M.2 #2.18 (3.3V)
unnamed: M.2 #2.70 (3.3V), M.2 #2.72 (3.3V), M.2 #2.74 (3.3V)
unnamed: M.2 #2.MP1, M.2 #2.MP2
unnamed: R62.2, Y1.1 (SBY)
unnamed: R65.1, U1.N7 (MGTRREF_115)
unnamed: R69.1, R70.1
unnamed: R73.1, R74.1
PCIe1_CKRQ: M.2 #1.52 (CLKREQ#), U1.B17 (IO_L20P_T3_18)
PCIe1_CLK_N: M.2 #1.53 (REFCLKn), R67.1, R70.2
PCIe1_CLK_P: M.2 #1.55 (REFCLKp), R68.1, R69.2
PCIe1_DET: M.2 #1.69 (PEDET), U1.A17 (IO_L20N_T3_18)
PCIe1_PERST: M.2 #1.54 (PEWAKE#), U1.C17 (IO_L19N_T3_VREF_18)
PCIe1_RCLK_N: C88.1, U1.J7 (MGTREFCLK0N_115)
PCIe1_RCLK_P: C87.1, U1.J8 (MGTREFCLK0P_115)
PCIe1_RX0_N: M.2 #1.41 (SATA-B+/PERn0), U1.M5 (MGTXRXN0_115)
PCIe1_RX0_P: M.2 #1.43 (SATA-B-/PERp0), U1.M6 (MGTXRXP0_115)
PCIe1_RX1_N: M.2 #1.29 (PERn1), U1.L3 (MGTXRXN1_115)
PCIe1_RX1_P: M.2 #1.31 (PERp1), U1.L4 (MGTXRXP1_115)
PCIe1_RX2_N: M.2 #1.17 (PERn2), U1.K5 (MGTXRXN2_115)
PCIe1_RX2_P: M.2 #1.19 (PERp2), U1.K6 (MGTXRXP2_115)
PCIe1_RX3_N: M.2 #1.5 (PERn3), U1.J3 (MGTXRXN3_115)
PCIe1_RX3_P: M.2 #1.7 (PERp3), U1.J4 (MGTXRXP3_115)
PCIe1_TX0_N: C95.1, U1.M1 (MGTXTXN0_115)
PCIe1_TX0_P: C93.1, U1.M2 (MGTXTXP0_115)
PCIe1_TX1_N: C99.1, U1.K1 (MGTXTXN1_115)
PCIe1_TX1_P: C97.1, U1.K2 (MGTXTXP1_115)
PCIe1_TX2_N: C103.1, U1.H1 (MGTXTXN2_115)
PCIe1_TX2_P: C101.1, U1.H2 (MGTXTXP2_115)
PCIe1_TX3_N: C107.1, U1.F1 (MGTXTXN3_115)
PCIe1_TX3_P: C105.1, U1.F2 (MGTXTXP3_115)
PCIe1_WAKE: M.2 #1.50 (PERST#), U1.B14 (IO_L17P_T2_18)
PCIe2_CKRQ: M.2 #2.52 (CLKREQ#), U1.A14 (IO_L17N_T2_18)
PCIe2_CLK_N: M.2 #2.55 (REFCLKp), R71.1, R74.2
PCIe2_CLK_P: M.2 #2.53 (REFCLKn), R72.1, R73.2
PCIe2_DET: M.2 #2.69 (PEDET), U1.D17 (IO_L19P_T3_18)
PCIe2_PERST: M.2 #2.50 (PERST#), U1.A16 (IO_L18N_T2_18)
PCIe2_RCLK_N: C92.1, U1.F5 (MGTREFCLK0N_116)
PCIe2_RCLK_P: C91.1, U1.F6 (MGTREFCLK0P_116)
PCIe2_RX0_N: M.2 #2.41 (SATA-B+/PERn0), U1.G3 (MGTXRXN0_116)
PCIe2_RX0_P: M.2 #2.43 (SATA-B-/PERp0), U1.G4 (MGTXRXP0_116)
PCIe2_RX1_N: M.2 #2.29 (PERn1), U1.E3 (MGTXRXN1_116)
PCIe2_RX1_P: M.2 #2.31 (PERp1), U1.E4 (MGTXRXP1_116)
PCIe2_RX2_N: M.2 #2.17 (PERn2), U1.D5 (MGTXRXN2_116)
PCIe2_RX2_P: M.2 #2.19 (PERp2), U1.D6 (MGTXRXP2_116)
PCIe2_RX3_N: M.2 #2.5 (PERn3), U1.C3 (MGTXRXN3_116)
PCIe2_RX3_P: M.2 #2.7 (PERp3), U1.C4 (MGTXRXP3_116)
PCIe2_TX0_N: C96.1, U1.D1 (MGTXTXN0_116)
PCIe2_TX0_P: C94.1, U1.D2 (MGTXTXP0_116)
PCIe2_TX1_N: C100.1, U1.B1 (MGTXTXN1_116)
PCIe2_TX1_P: C98.1, U1.B2 (MGTXTXP1_116)
PCIe2_TX2_N: C104.1, U1.A3 (MGTXTXN2_116)
PCIe2_TX2_P: C102.1, U1.A4 (MGTXTXP2_116)
PCIe2_TX3_N: C108.1, U1.B5 (MGTXTXN3_116)
PCIe2_TX3_P: C106.1, U1.B6 (MGTXTXP3_116)
PCIe2_WAKE: M.2 #2.54 (PEWAKE#), U1.A15 (IO_L18P_T2_18)
PWR_ALT: U1.D16 (IO_L14N_T2_SRCC_18)
PWR_SCL: U1.C16 (IO_L13N_T2_MRCC_18)
PWR_SDA: U1.E15 (IO_L14P_T2_SRCC_18)
Q1_RST: U1.G17 (IO_L10P_T1_18)
Q1_SEL: U1.C14 (IO_L16P_T2_18)
Q2_RST: U1.F17 (IO_L10N_T1_18)
Q2_SEL: U1.D14 (IO_L15N_T2_DQS_18)
Q3_RST: U1.E16 (IO_L11N_T1_SRCC_18)
Q3_SEL: U1.E14 (IO_L15P_T2_DQS_18)
Q4_RST: U1.F16 (IO_L11P_T1_SRCC_18)
Q4_SEL: U1.B15 (IO_L16N_T2_18)
Q_INT: R66.2, U1.H17 (IO_L8N_T1_18)
Q_SCL: U1.G14 (IO_L9N_T1_DQS_18)
Q_SDA: U1.H14 (IO_L9P_T1_DQS_18)
UART_RX: U1.H16 (IO_L8P_T1_18)
UART_TX: U1.H15 (IO_L7N_T1_18)
