cbalint13/m-blanc/hardware/mblanc_v0.3/kicad/m-blanc/schematic/5-QSFP.kicad_sch

## KiCad design hardware/mblanc_v0.3/kicad/m-blanc/schematic/5-QSFP.kicad_sch (2022-12-04)

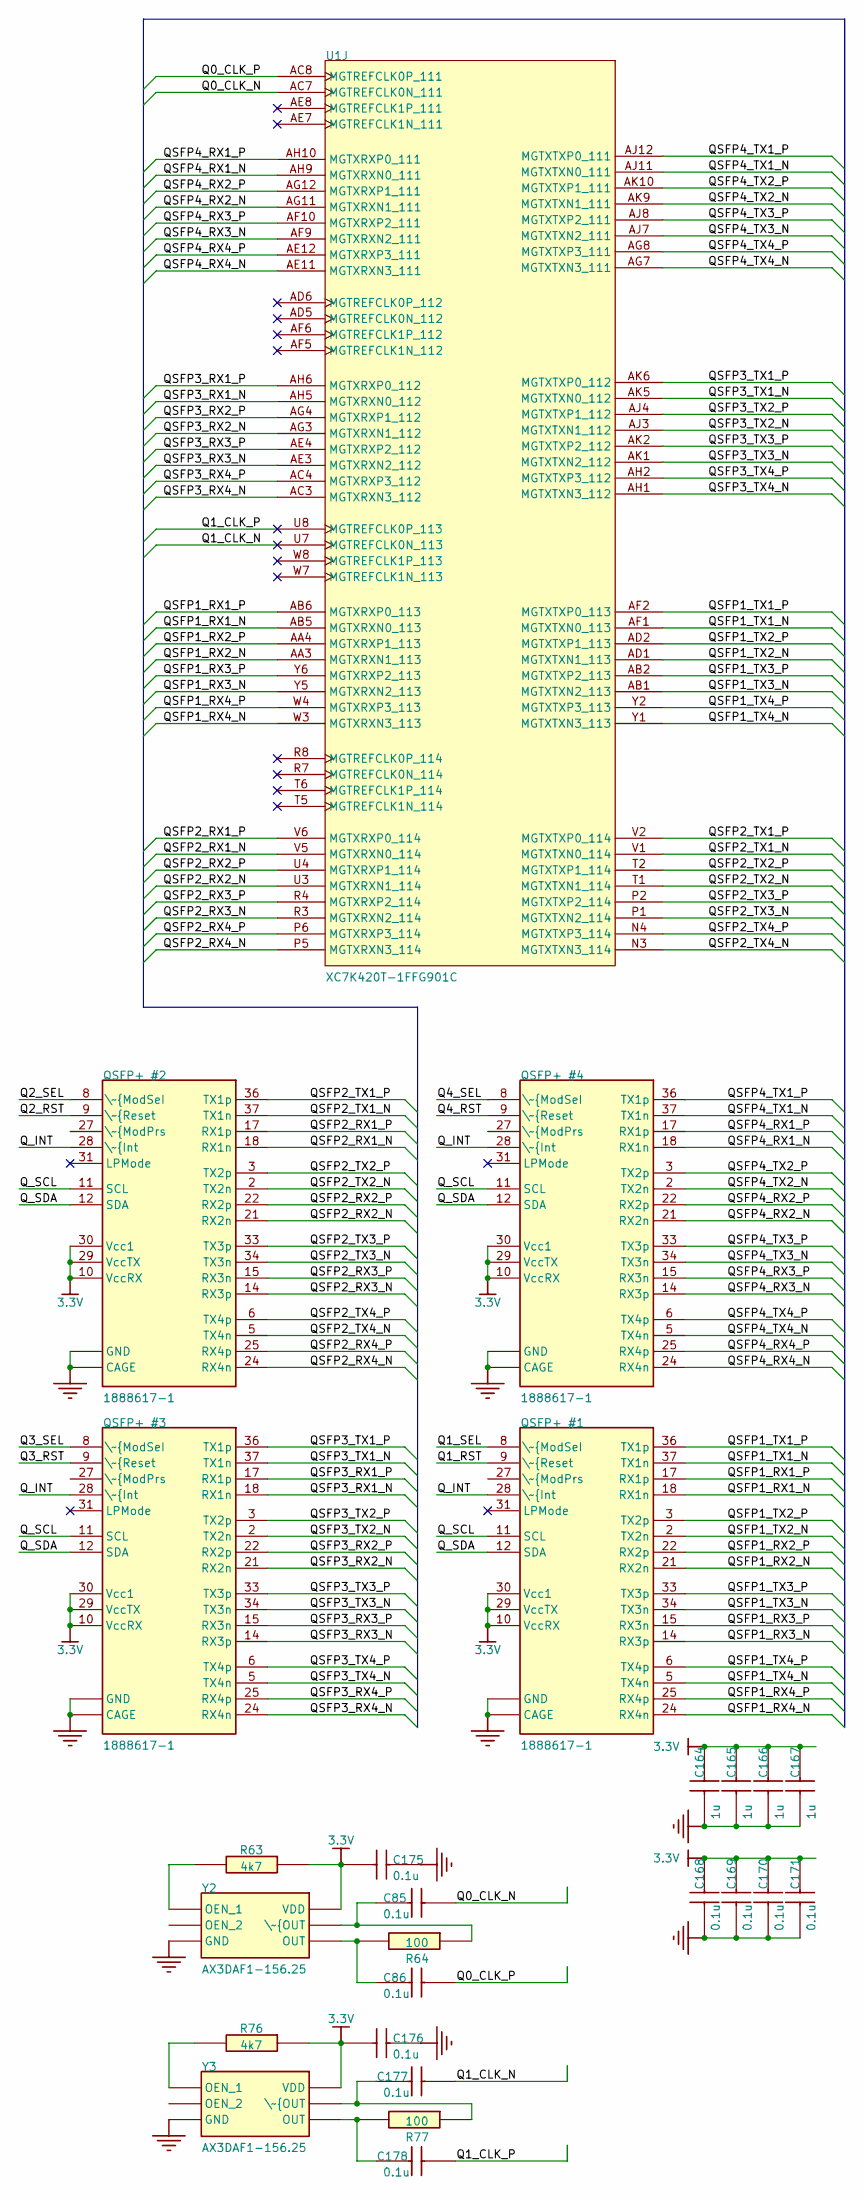
[picture p51: schematic 5-QSFP.kicad_sch]

Parts:
C85, C86, C168, C169, C170, C171, C175, C176, C177, C178: 0.1u; SMD0402
C164, C165, C166, C167: 1u; SMD0402
QSFP+ #1, QSFP+ #2, QSFP+ #3, QSFP+ #4: 1888617-1; 18886171; MANUFACTURER_PART_NUMBER 1888617-1; MOUSER PART NUMBER 571-1888617-1
R63, R76: 4k7; SMD0402
R64, R77: 100; SMD0402
U1: XC7K420T-1FFG901C; FFG901; PARTNUMBER XC7K420T-1FFG901C
Y2, Y3: AX3DAF1-156.25; AX3DAF11000000; MANUFACTURER_PART_NUMBER AX3DAF1-100.0000; MOUSER PART NUMBER 815-AX3DAF1-100.0000

Connections:
unnamed: C85.1, R64.1, Y2.5 (\~{OUT)
unnamed: C86.1, R64.2, Y2.4 (OUT)
unnamed: C164.1, C165.1, C166.1, C167.1
unnamed: C164.2, C165.2, C166.2, C167.2
unnamed: C168.1, C169.1, C170.1, C171.1
unnamed: C168.2, C169.2, C170.2, C171.2
unnamed: C175.1, R63.2, Y2.6 (VDD)
unnamed: C176.1, R76.2, Y3.6 (VDD)
unnamed: C177.1, R77.1, Y3.5 (\~{OUT)
unnamed: C178.1, R77.2, Y3.4 (OUT)
unnamed: QSFP+ #1.1 (GND), QSFP+ #1.4 (GND), QSFP+ #1.7 (GND), QSFP+ #1.13 (GND), QSFP+ #1.16 (GND), QSFP+ #1.19 (GND), QSFP+ #1.20 (GND), QSFP+ #1.23 (GND), QSFP+ #1.26 (GND), QSFP+ #1.32 (GND), QSFP+ #1.35 (GND), QSFP+ #1.38 (GND), QSFP+ #1.MH1 (CAGE), QSFP+ #1.MH2 (CAGE), QSFP+ #1.MH3 (CAGE), QSFP+ #1.MH4 (CAGE), QSFP+ #1.MH5 (CAGE), QSFP+ #1.MH6 (CAGE), QSFP+ #1.MH7 (CAGE), QSFP+ #1.MH8 (CAGE), QSFP+ #1.MH9 (CAGE), QSFP+ #1.MH10 (CAGE), QSFP+ #1.MH11 (CAGE), QSFP+ #1.MH12 (CAGE), QSFP+ #1.MH13 (CAGE), QSFP+ #1.MH14 (CAGE)
unnamed: QSFP+ #1.10 (VccRX), QSFP+ #1.29 (VccTX), QSFP+ #1.30 (Vcc1)
unnamed: QSFP+ #2.1 (GND), QSFP+ #2.4 (GND), QSFP+ #2.7 (GND), QSFP+ #2.13 (GND), QSFP+ #2.16 (GND), QSFP+ #2.19 (GND), QSFP+ #2.20 (GND), QSFP+ #2.23 (GND), QSFP+ #2.26 (GND), QSFP+ #2.32 (GND), QSFP+ #2.35 (GND), QSFP+ #2.38 (GND), QSFP+ #2.MH1 (CAGE), QSFP+ #2.MH2 (CAGE), QSFP+ #2.MH3 (CAGE), QSFP+ #2.MH4 (CAGE), QSFP+ #2.MH5 (CAGE), QSFP+ #2.MH6 (CAGE), QSFP+ #2.MH7 (CAGE), QSFP+ #2.MH8 (CAGE), QSFP+ #2.MH9 (CAGE), QSFP+ #2.MH10 (CAGE), QSFP+ #2.MH11 (CAGE), QSFP+ #2.MH12 (CAGE), QSFP+ #2.MH13 (CAGE), QSFP+ #2.MH14 (CAGE)
unnamed: QSFP+ #2.10 (VccRX), QSFP+ #2.29 (VccTX), QSFP+ #2.30 (Vcc1)
unnamed: QSFP+ #3.1 (GND), QSFP+ #3.4 (GND), QSFP+ #3.7 (GND), QSFP+ #3.13 (GND), QSFP+ #3.16 (GND), QSFP+ #3.19 (GND), QSFP+ #3.20 (GND), QSFP+ #3.23 (GND), QSFP+ #3.26 (GND), QSFP+ #3.32 (GND), QSFP+ #3.35 (GND), QSFP+ #3.38 (GND), QSFP+ #3.MH1 (CAGE), QSFP+ #3.MH2 (CAGE), QSFP+ #3.MH3 (CAGE), QSFP+ #3.MH4 (CAGE), QSFP+ #3.MH5 (CAGE), QSFP+ #3.MH6 (CAGE), QSFP+ #3.MH7 (CAGE), QSFP+ #3.MH8 (CAGE), QSFP+ #3.MH9 (CAGE), QSFP+ #3.MH10 (CAGE), QSFP+ #3.MH11 (CAGE), QSFP+ #3.MH12 (CAGE), QSFP+ #3.MH13 (CAGE), QSFP+ #3.MH14 (CAGE)
unnamed: QSFP+ #3.10 (VccRX), QSFP+ #3.29 (VccTX), QSFP+ #3.30 (Vcc1)
unnamed: QSFP+ #4.1 (GND), QSFP+ #4.4 (GND), QSFP+ #4.7 (GND), QSFP+ #4.13 (GND), QSFP+ #4.16 (GND), QSFP+ #4.19 (GND), QSFP+ #4.20 (GND), QSFP+ #4.23 (GND), QSFP+ #4.26 (GND), QSFP+ #4.32 (GND), QSFP+ #4.35 (GND), QSFP+ #4.38 (GND), QSFP+ #4.MH1 (CAGE), QSFP+ #4.MH2 (CAGE), QSFP+ #4.MH3 (CAGE), QSFP+ #4.MH4 (CAGE), QSFP+ #4.MH5 (CAGE), QSFP+ #4.MH6 (CAGE), QSFP+ #4.MH7 (CAGE), QSFP+ #4.MH8 (CAGE), QSFP+ #4.MH9 (CAGE), QSFP+ #4.MH10 (CAGE), QSFP+ #4.MH11 (CAGE), QSFP+ #4.MH12 (CAGE), QSFP+ #4.MH13 (CAGE), QSFP+ #4.MH14 (CAGE)
unnamed: QSFP+ #4.10 (VccRX), QSFP+ #4.29 (VccTX), QSFP+ #4.30 (Vcc1)
unnamed: R63.1, Y2.1 (OEN_1)
unnamed: R76.1, Y3.1 (OEN_1)
Q0_CLK_N: C85.2, U1.AC7 (MGTREFCLK0N_111)
Q0_CLK_P: C86.2, U1.AC8 (MGTREFCLK0P_111)
Q1_CLK_N: C177.2, U1.U7 (MGTREFCLK0N_113)
Q1_CLK_P: C178.2, U1.U8 (MGTREFCLK0P_113)
Q1_RST: QSFP+ #1.9 (\~{Reset)
Q1_SEL: QSFP+ #1.8 (\~{ModSeI)
Q2_RST: QSFP+ #2.9 (\~{Reset)
Q2_SEL: QSFP+ #2.8 (\~{ModSeI)
Q3_RST: QSFP+ #3.9 (\~{Reset)
Q3_SEL: QSFP+ #3.8 (\~{ModSeI)
Q4_RST: QSFP+ #4.9 (\~{Reset)
Q4_SEL: QSFP+ #4.8 (\~{ModSeI)
QSFP1_RX1_N: QSFP+ #1.18 (RX1n), U1.AB5 (MGTXRXN0_113)
QSFP1_RX1_P: QSFP+ #1.17 (RX1p), U1.AB6 (MGTXRXP0_113)
QSFP1_RX2_N: QSFP+ #1.21 (RX2n), U1.AA3 (MGTXRXN1_113)
QSFP1_RX2_P: QSFP+ #1.22 (RX2p), U1.AA4 (MGTXRXP1_113)
QSFP1_RX3_N: QSFP+ #1.14 (RX3p), U1.Y5 (MGTXRXN2_113)
QSFP1_RX3_P: QSFP+ #1.15 (RX3n), U1.Y6 (MGTXRXP2_113)
QSFP1_RX4_N: QSFP+ #1.24 (RX4n), U1.W3 (MGTXRXN3_113)
QSFP1_RX4_P: QSFP+ #1.25 (RX4p), U1.W4 (MGTXRXP3_113)
QSFP1_TX1_N: QSFP+ #1.37 (TX1n), U1.AF1 (MGTXTXN0_113)
QSFP1_TX1_P: QSFP+ #1.36 (TX1p), U1.AF2 (MGTXTXP0_113)
QSFP1_TX2_N: QSFP+ #1.2 (TX2n), U1.AD1 (MGTXTXN1_113)
QSFP1_TX2_P: QSFP+ #1.3 (TX2p), U1.AD2 (MGTXTXP1_113)
QSFP1_TX3_N: QSFP+ #1.34 (TX3n), U1.AB1 (MGTXTXN2_113)
QSFP1_TX3_P: QSFP+ #1.33 (TX3p), U1.AB2 (MGTXTXP2_113)
QSFP1_TX4_N: QSFP+ #1.5 (TX4n), U1.Y1 (MGTXTXN3_113)
QSFP1_TX4_P: QSFP+ #1.6 (TX4p), U1.Y2 (MGTXTXP3_113)
QSFP2_RX1_N: QSFP+ #2.18 (RX1n), U1.V5 (MGTXRXN0_114)
QSFP2_RX1_P: QSFP+ #2.17 (RX1p), U1.V6 (MGTXRXP0_114)
QSFP2_RX2_N: QSFP+ #2.21 (RX2n), U1.U3 (MGTXRXN1_114)
QSFP2_RX2_P: QSFP+ #2.22 (RX2p), U1.U4 (MGTXRXP1_114)
QSFP2_RX3_N: QSFP+ #2.14 (RX3p), U1.R3 (MGTXRXN2_114)
QSFP2_RX3_P: QSFP+ #2.15 (RX3n), U1.R4 (MGTXRXP2_114)
QSFP2_RX4_N: QSFP+ #2.24 (RX4n), U1.P5 (MGTXRXN3_114)
QSFP2_RX4_P: QSFP+ #2.25 (RX4p), U1.P6 (MGTXRXP3_114)
QSFP2_TX1_N: QSFP+ #2.37 (TX1n), U1.V1 (MGTXTXN0_114)
QSFP2_TX1_P: QSFP+ #2.36 (TX1p), U1.V2 (MGTXTXP0_114)
QSFP2_TX2_N: QSFP+ #2.2 (TX2n), U1.T1 (MGTXTXN1_114)
QSFP2_TX2_P: QSFP+ #2.3 (TX2p), U1.T2 (MGTXTXP1_114)
QSFP2_TX3_N: QSFP+ #2.34 (TX3n), U1.P1 (MGTXTXN2_114)
QSFP2_TX3_P: QSFP+ #2.33 (TX3p), U1.P2 (MGTXTXP2_114)
QSFP2_TX4_N: QSFP+ #2.5 (TX4n), U1.N3 (MGTXTXN3_114)
QSFP2_TX4_P: QSFP+ #2.6 (TX4p), U1.N4 (MGTXTXP3_114)
QSFP3_RX1_N: QSFP+ #3.18 (RX1n), U1.AH5 (MGTXRXN0_112)
QSFP3_RX1_P: QSFP+ #3.17 (RX1p), U1.AH6 (MGTXRXP0_112)
QSFP3_RX2_N: QSFP+ #3.21 (RX2n), U1.AG3 (MGTXRXN1_112)
QSFP3_RX2_P: QSFP+ #3.22 (RX2p), U1.AG4 (MGTXRXP1_112)
QSFP3_RX3_N: QSFP+ #3.14 (RX3p), U1.AE3 (MGTXRXN2_112)
QSFP3_RX3_P: QSFP+ #3.15 (RX3n), U1.AE4 (MGTXRXP2_112)
QSFP3_RX4_N: QSFP+ #3.24 (RX4n), U1.AC3 (MGTXRXN3_112)
QSFP3_RX4_P: QSFP+ #3.25 (RX4p), U1.AC4 (MGTXRXP3_112)
QSFP3_TX1_N: QSFP+ #3.37 (TX1n), U1.AK5 (MGTXTXN0_112)
QSFP3_TX1_P: QSFP+ #3.36 (TX1p), U1.AK6 (MGTXTXP0_112)
QSFP3_TX2_N: QSFP+ #3.2 (TX2n), U1.AJ3 (MGTXTXN1_112)
QSFP3_TX2_P: QSFP+ #3.3 (TX2p), U1.AJ4 (MGTXTXP1_112)
QSFP3_TX3_N: QSFP+ #3.34 (TX3n), U1.AK1 (MGTXTXN2_112)
QSFP3_TX3_P: QSFP+ #3.33 (TX3p), U1.AK2 (MGTXTXP2_112)
QSFP3_TX4_N: QSFP+ #3.5 (TX4n), U1.AH1 (MGTXTXN3_112)
QSFP3_TX4_P: QSFP+ #3.6 (TX4p), U1.AH2 (MGTXTXP3_112)
QSFP4_RX1_N: QSFP+ #4.18 (RX1n), U1.AH9 (MGTXRXN0_111)
QSFP4_RX1_P: QSFP+ #4.17 (RX1p), U1.AH10 (MGTXRXP0_111)
QSFP4_RX2_N: QSFP+ #4.21 (RX2n), U1.AG11 (MGTXRXN1_111)
QSFP4_RX2_P: QSFP+ #4.22 (RX2p), U1.AG12 (MGTXRXP1_111)
QSFP4_RX3_N: QSFP+ #4.14 (RX3p), U1.AF9 (MGTXRXN2_111)
QSFP4_RX3_P: QSFP+ #4.15 (RX3n), U1.AF10 (MGTXRXP2_111)
QSFP4_RX4_N: QSFP+ #4.24 (RX4n), U1.AE11 (MGTXRXN3_111)
QSFP4_RX4_P: QSFP+ #4.25 (RX4p), U1.AE12 (MGTXRXP3_111)
QSFP4_TX1_N: QSFP+ #4.37 (TX1n), U1.AJ11 (MGTXTXN0_111)
QSFP4_TX1_P: QSFP+ #4.36 (TX1p), U1.AJ12 (MGTXTXP0_111)
QSFP4_TX2_N: QSFP+ #4.2 (TX2n), U1.AK9 (MGTXTXN1_111)
QSFP4_TX2_P: QSFP+ #4.3 (TX2p), U1.AK10 (MGTXTXP1_111)
QSFP4_TX3_N: QSFP+ #4.34 (TX3n), U1.AJ7 (MGTXTXN2_111)
QSFP4_TX3_P: QSFP+ #4.33 (TX3p), U1.AJ8 (MGTXTXP2_111)
QSFP4_TX4_N: QSFP+ #4.5 (TX4n), U1.AG7 (MGTXTXN3_111)
QSFP4_TX4_P: QSFP+ #4.6 (TX4p), U1.AG8 (MGTXTXP3_111)
Q_INT: QSFP+ #1.28 (\~{Int), QSFP+ #2.28 (\~{Int), QSFP+ #3.28 (\~{Int), QSFP+ #4.28 (\~{Int)
Q_SCL: QSFP+ #1.11 (SCL), QSFP+ #2.11 (SCL), QSFP+ #3.11 (SCL), QSFP+ #4.11 (SCL)
Q_SDA: QSFP+ #1.12 (SDA), QSFP+ #2.12 (SDA), QSFP+ #3.12 (SDA), QSFP+ #4.12 (SDA)
